pdsmart/MZ80A_RFS/docs/20200314152534.png

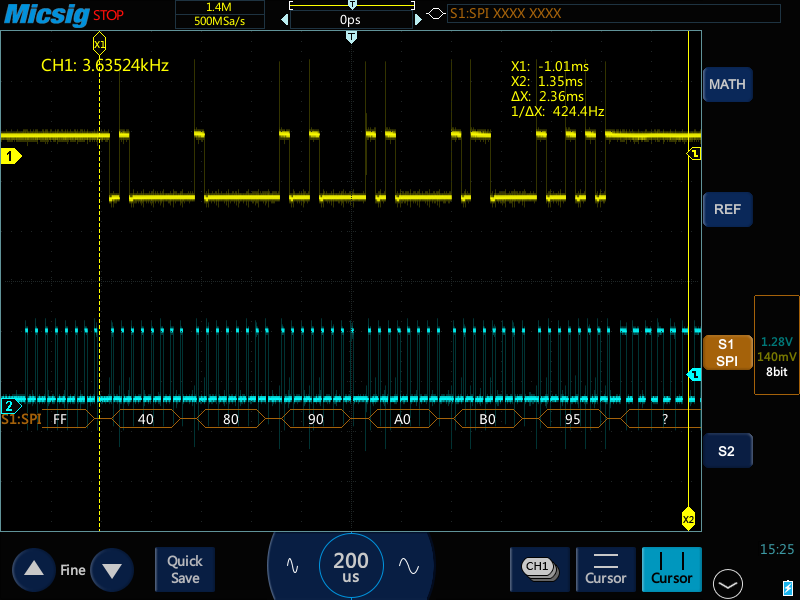
docs/20200314152534.png
