pdsmart/MZ80A_RFS/software/asm/RFSBASIC.asm

;-----------------------------------------------------------------------------------------------
; NASCOM ROM BASIC Ver 4.7, (C) 1978 Microsoft
; Scanned from source published in 80-BUS NEWS from Vol 2, Issue 3
; (May-June 1983) to Vol 3, Issue 3 (May-June 1984)
; Adapted for the freeware Zilog Macro Assembler 2.10 to produce
; the original ROM code (checksum A934H). PA
;
; This BASIC has been created from the original NASCOM v4.7b source and also
; may have elements of Grant Searle's changes as both were used in creating this
; version.
;
; It has undergone extensive modification:
; 1. Restore the CLOAD/CSAVE commands. These commands load/save tokenised cassette
;    images. The cassette images are from the NASCOM but converted with the
;    'nasconv' C program which removes the tape formatting, updates the token values
;    and address pointers.
; 2. Add LOAD/SAVE commands. These commands load/save BASIC in text format.
; 3. Restored the SCREEN command so it works with the Sharp MZ80A 40/80 column screen.
; 4. Increased the command word table to allow additional commands which I expect to add.
; I've added additional comments as things have been figured out to aid future understanding.
;
; Thus (C)opyright notices:
; Original source is: (C) 1978 Microsoft
; Updates (some reversed out): Grant Searle, http://searle.hostei.com/grant/index.html
;                                            eMail: home.micros01@btinternet.com
; All other updates (C) Philip Smart, 2020. http://www.eaw.app philip.smart\@net2net.org
;-----------------------------------------------------------------------------------------------


            ; Bring in additional resources.
            INCLUDE "BASIC_Definitions.asm"
            INCLUDE "Macros.asm"

            ; Sharp MZ-80A Tape Format Header - used by all software including RFS/TZFS 
            ; in processing/loading of this file.
            ;
            ORG     10F0h

            DB      01h                                                                                     ; Code Type, 01 = Machine Code.
HEADER1:    IF BUILD_MZ80A = 1
            DB      "MZ80A BASIC V1.1", 0DH                                                                 ; Title/Name (17 bytes).
            DW      CODEEND - CODESTART                                                                     ; Size of program.
            DW      CODESTART                                                                               ; Load address of program.
            DW      CODESTART                                                                               ; Exec address of program.
            ENDIF

HEADER2:    IF BUILD_RFS = 1
            DB      "RFS BASIC V1.1" , 0DH, 0DH, 0DH                                                        ; Title/Name (17 bytes).
            DW      (CODEEND - CODESTART) + (RELOCEND - RELOC) + (RELOCRFS2END - RELOCRFS2)                 ; Size of program.
            DW      01200H                                                                                  ; Load address of program.
            DW      RELOCRFS                                                                                ; Exec address of program.
            ENDIF

HEADER3:    IF BUILD_TZFS = 1
            DB      "RFS BASIC V1.1 ", 0DH, 0DH                                                             ; Title/Name (17 bytes).
            DW      (CODEEND - CODESTART) + (RELOCEND - RELOC)                                              ; Size of program.
            DW      01200H                                                                                  ; Load address of program.
            DW      RELOC                                                                                   ; Exec address of program.
            ENDIF

            DB      00h, 00h, 00h, 00h, 00h, 00h, 00h, 00h, 00h, 00h, 00h, 00h, 00h, 00h, 00h, 00h          ; Comment (104 bytes).
            DB      00h, 00h, 00h, 00h, 00h, 00h, 00h, 00h, 00h, 00h, 00h, 00h, 00h, 00h, 00h, 00h
            DB      00h, 00h, 00h, 00h, 00h, 00h, 00h, 00h, 00h, 00h, 00h, 00h, 00h, 00h, 00h, 00h
            DB      00h, 00h, 00h, 00h, 00h, 00h, 00h, 00h, 00h, 00h, 00h, 00h, 00h, 00h, 00h, 00h
            DB      00h, 00h, 00h, 00h, 00h, 00h, 00h, 00h, 00h, 00h, 00h, 00h, 00h, 00h, 00h, 00h
            DB      00h, 00h, 00h, 00h, 00h, 00h, 00h, 00h, 00h, 00h, 00h, 00h, 00h, 00h, 00h, 00h
            DB      00h, 00h, 00h, 00h, 00h, 00h, 00h, 00h

            ; Load address of this program when first loaded.
            ;
BUILD1:     IF BUILD_MZ80A = 1
            ORG     1200H
            ENDIF

BUILD2:     IF BUILD_TZFS+BUILD_RFS > 0
            ORG     0000H
            ENDIF

CODESTART:

COLD:       JP      STARTB               ; Jump for cold start
WARM:       JP      WARMST               ; Jump for warm start
STARTB:     
            LD      IX,0                 ; Flag cold start
            JP      CSTART               ; Jump to initialise

            DW      DEINT                ; Get integer -32768 to 32767
            DW      ABPASS               ; Return integer in AB


VECTORS:    IF BUILD_TZFS+BUILD_RFS > 0
            ALIGN   0038H
            ORG     0038H
INTVEC:     DS      3                    ; Space for the Interrupt vector.

            ALIGN   0066H
            ORG     0066H
NMIVEC:     DS      3                    ; Space for the NMI vector.
            ENDIF

CSTART:     DI                           ; Disable Interrupts and sat mode. NB. Interrupts are physically disabled by 8255 Port C2 set to low.
            IM      1
            LD      SP,STACK             ; Start of workspace RAM

MEMSW0:     IF BUILD_TZFS+BUILD_RFS > 0
            LD      A,TZMM_MZ700_0       ; Ensure the top part of RAM is set to use the mainboard as we need to configure hardware.
            OUT     (MMCFG),A
            ENDIF

INITST:     LD      A,0                  ; Clear break flag
            LD      (BRKFLG),A

            LD      HL,GVARSTART         ; Start of global variable area
            LD      BC,GVAREND-GVARSTART ; Size of global variable area.
            XOR     A
            LD      D,A
INIT1:      LD      (HL),D               ; Clear variable memory including stack space.
            INC     HL
            DEC     BC
            LD      A,B
            OR      C
            JR      NZ,INIT1
            ;
            CALL    MODE                 ; Configure 8255 port C, set Motor Off, VGATE to 1 (off) and INTMSK to 0 (interrupts disabled).
            LD      A,000H               ; Clear the screen buffer.
            LD      HL,SCRN
            CALL    CLR8
            LD      A,017H               ; Blue background, white characters in colour mode. Bit 7 is set as a write to bit 7 @ DFFFH selects 80Char mode.
            LD      HL,ARAM
            CALL    CLR8
            LD      A,004H
            LD      (TEMPW),A            ; Setup the tempo for sound output.

INIT3:      ; Setup keyboard buffer control.
            LD      A,0
            LD      (KEYCOUNT),A         ; Set keyboard buffer to empty.
            LD      HL,KEYBUF
            LD      (KEYWRITE),HL        ; Set write pointer to beginning of keyboard buffer.
            LD      (KEYREAD),HL         ; Set read pointer to beginning of keyboard buffer.

            ; Setup keyboard rate control and set to CAPSLOCK mode.
            ; (0 = Off, 1 = CAPSLOCK, 2 = SHIFTLOCK).
            LD      A,000H               ; Initialise key repeater.
            LD      (KEYRPT),A
            LD      A,001H
            LD      (SFTLK),A            ; Setup shift lock, default = off.

            ; Setup the initial cursor, for CAPSLOCK this is a double underscore.
            LD      A,03EH
            LD      (FLSDT),A
            LD      A,080H               ; Cursor on (Bit D7=1).
            LD      (FLASHCTL),A

            ; Change to 80 character mode.
            LD      HL,DSPCTL            ; Setup address of display control register latch.
            LD      A, 128               ; 80 char mode.
            LD      E,(HL)               ; Dummy operation to enable latch write via multivibrator.
            LD      (HL), A
            CALL    MLDSP
            CALL    BEL                  ; Beep to indicate startup - for cases where screen is slow to startup.
            LD      A,0FFH
            LD      (SWRK),A

INITANSI:   IF INCLUDE_ANSITERM = 1      ; If the ansi terminal emulator is builtin, enable it as default.
            LD      (ANSIENABLE),A
            ENDIF

            ; Setup timer interrupts
            LD      IX,TIMIN             ; Pass the interrupt service handler vector.
            LD      BC,00000H            ; Time starts at 00:00:00 01/01/1980 on initialisation.
            LD      DE,00000H
            LD      HL,00000H
            CALL    TIMESET
            ;
            LD      A,05H                ; Enable interrupts at hardware level, this must be done before switching memory mode.
            LD      (KEYPF),A
            ;
MEMSW1:     IF BUILD_TZFS+BUILD_RFS > 0
            LD      A,TZMM_MZ700_2       ; Enable the full 64K memory range before starting BASIC initialisation.
            OUT     (MMCFG),A
            ENDIF

            ; Clear memory
            LD      HL,WRKSPC
MEMSZ1:     IF BUILD_MZ80A = 1
            LD      BC,MAXMEM - WRKSPC   ; Clear to top of physical RAM.
            ENDIF
MEMSZ2:     IF BUILD_TZFS+BUILD_RFS > 0
            LD      BC,10000H - WRKSPC   ; Clear to top of physical RAM.
            ENDIF
            LD      E,00H
INIT4:      LD      (HL),E
            INC     HL
            DEC     BC
            LD      A,B
            OR      C
            JR      NZ,INIT4
            ;
            EI
            ;
INIT:       LD      DE,INITAB            ; Initialise workspace
            LD      B,INITBE-INITAB+3    ; Bytes to copy
            LD      HL,WRKSPC            ; Into workspace RAM
COPY:       LD      A,(DE)               ; Get source
            LD      (HL),A               ; To destination
            INC     HL                   ; Next destination
            INC     DE                   ; Next source
            DEC     B                    ; Count bytes
            JP      NZ,COPY              ; More to move
       ;    LD      SP,HL                ; Temporary stack
            CALL    CLREG                ; Clear registers and stack
            CALL    PRNTCRLF             ; Output CRLF
            LD      (BUFFER+72+1),A      ; Mark end of buffer
            LD      (PROGST),A           ; Initialise program area

            LD      HL,MAXMEM
            LD      DE,0-50              ; 50 Bytes string space
            LD      (LSTRAM),HL          ; Save last available RAM
            ADD     HL,DE                ; Allocate string space
            LD      (STRSPC),HL          ; Save string space
            CALL    CLRPTR               ; Clear program area
            LD      HL,(STRSPC)          ; Get end of memory
            LD      DE,0-17              ; Offset for free bytes
            ADD     HL,DE                ; Adjust HL
            LD      DE,PROGST            ; Start of program text
            LD      A,L                  ; Get LSB
            SUB     E                    ; Adjust it
            LD      L,A                  ; Re-save
            LD      A,H                  ; Get MSB
            SBC     A,D                  ; Adjust it
            LD      H,A                  ; Re-save
            PUSH    HL                   ; Save bytes free
            CALL    CLS                  ; Clear screen and initialise the screen variables
            LD      HL,SIGNON            ; Sign-on message
            CALL    PRS                  ; Output string
            POP     HL                   ; Get bytes free back
            CALL    PRNTHL               ; Output amount of free memory
            LD      HL,BFREE             ; " Bytes free" message
            CALL    PRS                  ; Output string

WARMST:     LD      SP,STACK             ; Temporary stack
BRKRET:     CALL    CLREG                ; Clear registers and stack
            JP      PRNTOK               ; Go to get command line

            ; FUNCTION ADDRESS TABLE

FNCTAB:     DW      SGN
            DW      INT
            DW      ABS
            DW      USR
            DW      FRE
            DW      INP
            DW      POS
            DW      SQR
            DW      RND
            DW      LOG
            DW      EXP
            DW      COS
            DW      SIN
            DW      TAN
            DW      ATN
            DW      PEEK
            DW      DEEK
            DW      POINT
            DW      LEN
            DW      STR
            DW      VAL
            DW      ASC
            DW      CHR
            DW      HEX
            DW      BIN
            DW      LEFT
            DW      RIGHT
            DW      MID

            ; RESERVED WORD LIST

WORDS:      DB      'E'+80H,"ND"         ; 0x80
            DB      'F'+80H,"OR"         ; 0x81
            DB      'N'+80H,"EXT"        ; 0x82
            DB      'D'+80H,"ATA"        ; 0x83
            DB      'I'+80H,"NPUT"       ; 0x84
            DB      'D'+80H,"IM"         ; 0x85
            DB      'R'+80H,"EAD"        ; 0x86
            DB      'L'+80H,"ET"         ; 0x87
            DB      'G'+80H,"OTO"        ; 0x88
            DB      'R'+80H,"UN"         ; 0x89
            DB      'I'+80H,"F"          ; 0x8a
            DB      'R'+80H,"ESTORE"     ; 0x8b
            DB      'G'+80H,"OSUB"       ; 0x8c
            DB      'R'+80H,"ETURN"      ; 0x8d
            DB      'R'+80H,"EM"         ; 0x8e
            DB      'S'+80H,"TOP"        ; 0x8f
            DB      'O'+80H,"UT"         ; 0x90
            DB      'O'+80H,"N"          ; 0x91
            DB      'N'+80H,"ULL"        ; 0x92
            DB      'W'+80H,"AIT"        ; 0x93
            DB      'D'+80H,"EF"         ; 0x94
            DB      'P'+80H,"OKE"        ; 0x95
            DB      'D'+80H,"OKE"        ; 0x96
            DB      'S'+80H,"CREEN"      ; 0x97
            DB      'L'+80H,"INES"       ; 0x98
            DB      'C'+80H,"LS"         ; 0x99
            DB      'W'+80H,"IDTH"       ; 0x9a
            DB      'M'+80H,"ONITOR"     ; 0x9b
            DB      'S'+80H,"ET"         ; 0x9c
            DB      'R'+80H,"ESET"       ; 0x9d
            DB      'P'+80H,"RINT"       ; 0x9e
            DB      'C'+80H,"ONT"        ; 0x9f
            DB      'L'+80H,"IST"        ; 0xa0
            DB      'C'+80H,"LEAR"       ; 0xa1
            DB      'A'+80H,"NSITERM"    ; 0xa2

            ; Optional commands to be builtin when a tranZPUter board is present.
OPTIONS0:   IF BUILD_TZFS = 1
              DB    'C'+80H,"LOAD"       ; 0xa3
              DB    'C'+80H,"SAVE"       ; 0xa4
              DB    'L'+80H,"OAD"        ; 0xa5
              DB    'S'+80H,"AVE"        ; 0xa6 
              DB    'F'+80H,"REQ"        ; 0xa7
              DB    'D'+80H,"IR"         ; 0xa8  
              DB    'C'+80H,"D"          ; 0xa9 
            ENDIF
            IF BUILD_RFS = 1
              DB    'C'+80H,"LOAD"       ; 0xa3
              DB    'C'+80H,"SAVE"       ; 0xa4
              DB    'R'+80H,"EM"         ; 0xa5  
              DB    'R'+80H,"EM"         ; 0xa6  
              DB    'R'+80H,"EM"         ; 0xa7  
              DB    'R'+80H,"EM"         ; 0xa8  
              DB    'R'+80H,"EM"         ; 0xa9  
            ENDIF
            IF BUILD_MZ80A = 1
              DB    'C'+80H,"LOAD"       ; 0xa3
              DB    'C'+80H,"SAVE"       ; 0xa4
              DB    'R'+80H,"EM"         ; 0xa5  
              DB    'R'+80H,"EM"         ; 0xa6  
              DB    'R'+80H,"EM"         ; 0xa7  
              DB    'R'+80H,"EM"         ; 0xa8  
              DB    'R'+80H,"EM"         ; 0xa9  
            ENDIF
            DB      'N'+80H,"EW"         ; 0xaa    <- Command list terminator word, move to lowest command. Update the ZNEW variable below as well.
                                         ;         <- Reserved space for new commands.
            DB      'R'+80H,"EM"         ; 0xab  
            DB      'R'+80H,"EM"         ; 0xac  
            DB      'R'+80H,"EM"         ; 0xad  
            DB      'R'+80H,"EM"         ; 0xae  
            DB      'R'+80H,"EM"         ; 0xaf  
            DB      'R'+80H,"EM"         ; 0xb0  
            DB      'R'+80H,"EM"         ; 0xb1  
            DB      'R'+80H,"EM"         ; 0xb2  
            DB      'R'+80H,"EM"         ; 0xb3  
            DB      'R'+80H,"EM"         ; 0xb4  
            DB      'R'+80H,"EM"         ; 0xb5  
            DB      'R'+80H,"EM"         ; 0xb6  
            DB      'R'+80H,"EM"         ; 0xb7  
            DB      'R'+80H,"EM"         ; 0xb8  
            DB      'R'+80H,"EM"         ; 0xb9  
            DB      'R'+80H,"EM"         ; 0xba  
            DB      'R'+80H,"EM"         ; 0xbb  
            DB      'R'+80H,"EM"         ; 0xbc  
            DB      'R'+80H,"EM"         ; 0xbd  
            DB      'R'+80H,"EM"         ; 0xbe  
            DB      'R'+80H,"EM"         ; 0xbf  

            DB      'T'+80H,"AB("        ; 0xc0  <- 0xa5
            DB      'T'+80H,"O"          ; 0xc1  <- 0xa6
            DB      'F'+80H,"N"          ; 0xc2  <- 0xa7
            DB      'S'+80H,"PC("        ; 0xc3  <- 0xa8
            DB      'T'+80H,"HEN"        ; 0xc4  <- 0xa9
            DB      'N'+80H,"OT"         ; 0xc5  <- 0xaa
            DB      'S'+80H,"TEP"        ; 0xc6  <- 0xab

            DB      '+'+80H              ; 0xc7  <- 0xac
            DB      '-'+80H              ; 0xc8  <- 0xad
            DB      '*'+80H              ; 0xc9  <- 0xae
            DB      '/'+80H              ; 0xca  <- 0xaf
            DB      '^'+80H              ; 0xcb  <- 0xb0
            DB      'A'+80H,"ND"         ; 0xcc  <- 0xb1
            DB      'O'+80H,"R"          ; 0xcd  <- 0xb2
            DB      '>'+80H              ; 0xce  <- 0xb3
            DB      '='+80H              ; 0xcf  <- 0xb4
            DB      '<'+80H              ; 0xd0  <- 0xb5

            DB      'S'+80H,"GN"         ; 0xd1  <- 0xb6
            DB      'I'+80H,"NT"         ; 0xd2  <- 0xb7
            DB      'A'+80H,"BS"         ; 0xd3  <- 0xb8
            DB      'U'+80H,"SR"         ; 0xd4  <- 0xb9
            DB      'F'+80H,"RE"         ; 0xd5  <- 0xba
            DB      'I'+80H,"NP"         ; 0xd6  <- 0xbb
            DB      'P'+80H,"OS"         ; 0xd7  <- 0xbc
            DB      'S'+80H,"QR"         ; 0xd8  <- 0xbd
            DB      'R'+80H,"ND"         ; 0xd9  <- 0xbe
            DB      'L'+80H,"OG"         ; 0xda  <- 0xbf
            DB      'E'+80H,"XP"         ; 0xdb  <- 0xc0
            DB      'C'+80H,"OS"         ; 0xdc  <- 0xc1
            DB      'S'+80H,"IN"         ; 0xdd  <- 0xc2
            DB      'T'+80H,"AN"         ; 0xde  <- 0xc3
            DB      'A'+80H,"TN"         ; 0xdf  <- 0xc4
            DB      'P'+80H,"EEK"        ; 0xe0  <- 0xc5
            DB      'D'+80H,"EEK"        ; 0xe1  <- 0xc6
            DB      'P'+80H,"OINT"       ; 0xe2  <- 0xc7
            DB      'L'+80H,"EN"         ; 0xe3  <- 0xc8
            DB      'S'+80H,"TR$"        ; 0xe4  <- 0xc9
            DB      'V'+80H,"AL"         ; 0xe5  <- 0xca
            DB      'A'+80H,"SC"         ; 0xe6  <- 0xcb
            DB      'C'+80H,"HR$"        ; 0xe7  <- 0xcc
            DB      'H'+80H,"EX$"        ; 0xe8  <- 0xcd
            DB      'B'+80H,"IN$"        ; 0xe9  <- 0xce
            DB      'L'+80H,"EFT$"       ; 0xea  <- 0xcf
            DB      'R'+80H,"IGHT$"      ; 0xeb  <- 0xd0
            DB      'M'+80H,"ID$"        ; 0xec  <- 0xd1
            DB      80H                  ; End of list marker

            ; KEYWORD ADDRESS TABLE

WORDTB:     DW      PEND
            DW      FOR
            DW      NEXT
            DW      DATA
            DW      INPUT
            DW      DIM
            DW      READ
            DW      LET
            DW      GOTO
            DW      RUN
            DW      IF
            DW      RESTOR
            DW      GOSUB
            DW      RETURN
            DW      REM
            DW      STOP
            DW      POUT
            DW      ON
            DW      NULL
            DW      WAIT
            DW      DEF
            DW      POKE
            DW      DOKE
            DW      SCREEN
            DW      LINES
            DW      CLS
            DW      WIDTH
            DW      MONITR
            DW      PSET
            DW      RESET
            DW      PRINT
            DW      CONT
            DW      LIST
            DW      CLEAR
            DW      SETANSITERM          ; Enable/disable the ANSI Terminal Emulator.

            ; Optional commands to be builtin when a tranZPUter board is present.
OPTIONS1:   IF BUILD_TZFS = 1
            DW      CLOADTZ              ; Load tokenised BASIC program.
            DW      CSAVETZ              ; Save tokenised BASIC program.
            DW      LOAD                 ; Load ASCII text BASIC program.
            DW      SAVE                 ; Save BASIC as ASCII text.
            DW      SETFREQ              ; Set the CPU Frequency.    
            DW      DIRSDCARD            ; List out the SD directory.
            DW      SETDIR               ; Change directory for all load and save operations.
            ENDIF
OPTIONS2:   IF BUILD_RFS = 1
            DW      CLOAD80A             ; Load tokenised BASIC program from tape.
            DW      CSAVE80A             ; Save tokenised BASIC program to tape.
            DW      REM
            DW      REM
            DW      REM
            DW      REM
            DW      REM
            ENDIF
OPTIONS3:   IF BUILD_MZ80A = 1
            DW      CLOAD80A             ; Load tokenised BASIC program from tape.
            DW      CSAVE80A             ; Save tokenised BASIC program to tape.
            DW      REM
            DW      REM
            DW      REM
            DW      REM
            DW      REM
            ENDIF
            DW      NEW

            ; RESERVED WORD TOKEN VALUES

ZEND        EQU     080H                 ; END    - ZEND marks the start of the table.
ZFOR        EQU     081H                 ; FOR
ZDATA       EQU     083H                 ; DATA
ZGOTO       EQU     088H                 ; GOTO
ZGOSUB      EQU     08CH                 ; GOSUB
ZREM        EQU     08EH                 ; REM
ZPRINT      EQU     09EH                 ; PRINT
ZNEW        EQU     0AAH                 ; NEW    - ZNEW marks the end of the table
                                         ; AA..BF are reserved for future commands.

            ; Space for expansion, a block of tokens for commands has been created from 0xA5 to 0xBF.

FUNCSTRT    EQU     0C0H                 ; Function start.
ZTAB        EQU     FUNCSTRT + 00H       ; 0A5H            ; TAB
ZTO         EQU     FUNCSTRT + 01H       ; 0A6H            ; TO
ZFN         EQU     FUNCSTRT + 02H       ; 0A7H            ; FN
ZSPC        EQU     FUNCSTRT + 03H       ; 0A8H            ; SPC
ZTHEN       EQU     FUNCSTRT + 04H       ; 0A9H            ; THEN
ZNOT        EQU     FUNCSTRT + 05H       ; 0AAH            ; NOT
ZSTEP       EQU     FUNCSTRT + 06H       ; 0ABH            ; STEP

ZPLUS       EQU     FUNCSTRT + 07H       ; 0ACH            ; +
ZMINUS      EQU     FUNCSTRT + 08H       ; 0ADH            ; -
ZTIMES      EQU     FUNCSTRT + 09H       ; 0AEH            ; *
ZDIV        EQU     FUNCSTRT + 0AH       ; 0AFH            ; /
                                         ; 0B0H
                                         ; 0B1H
ZOR         EQU     FUNCSTRT + 0dH       ; 0B2H            ; OR
ZGTR        EQU     FUNCSTRT + 0eH       ; 0B3H            ; >
ZEQUAL      EQU     FUNCSTRT + 0fH       ; 0B4H            ; M
ZLTH        EQU     FUNCSTRT + 10H       ; 0B5H            ; <
ZSGN        EQU     FUNCSTRT + 11H       ; 0B6H            ; SGN
                                         ; 0B7H
                                         ; 0B8H
                                         ; 0B9H
                                         ; 0BAH
                                         ; 0BBH
                                         ; 0BCH
                                         ; 0BDH
                                         ; 0BEH
                                         ; 0BFH
                                         ; 0C0H
                                         ; 0C1H
                                         ; 0C2H
                                         ; 0C3H
                                         ; 0C4H
                                         ; 0C5H
                                         ; 0C6H
ZPOINT      EQU     FUNCSTRT + 22H       ; 0C7H            ; POINT
                                         ; 0C8H
                                         ; 0C9H
                                         ; 0CAH
                                         ; 0CBH
                                         ; 0CCH
ZLEFT       EQU     FUNCSTRT + 2aH       ; 0CFH            ; LEFT$

            ; Space for expansion, reserve a block of tokens for functions.


            ; ARITHMETIC PRECEDENCE TABLE

PRITAB:     DB      79H                  ; Precedence value
            DW      PADD                 ; FPREG = <last> + FPREG

            DB      79H                  ; Precedence value
            DW      PSUB                 ; FPREG = <last> - FPREG

            DB      7CH                  ; Precedence value
            DW      MULT                 ; PPREG = <last> * FPREG

            DB      7CH                  ; Precedence value
            DW      DIV                  ; FPREG = <last> / FPREG

            DB      7FH                  ; Precedence value
            DW      POWER                ; FPREG = <last> ^ FPREG

            DB      50H                  ; Precedence value
            DW      PAND                 ; FPREG = <last> AND FPREG

            DB      46H                  ; Precedence value
            DW      POR                  ; FPREG = <last> OR FPREG

            ; BASIC ERROR CODE LIST

ERRORS:     DB      "NF"                 ; NEXT without FOR
            DB      "SN"                 ; Syntax error
            DB      "RG"                 ; RETURN without GOSUB
            DB      "OD"                 ; Out of DATA
            DB      "FC"                 ; Illegal function call
            DB      "OV"                 ; Overflow error
            DB      "OM"                 ; Out of memory
            DB      "UL"                 ; Undefined line
            DB      "BS"                 ; Bad subscript
            DB      "DD"                 ; Re-DIMensioned array
            DB      "/0"                 ; Division by zero
            DB      "ID"                 ; Illegal direct
            DB      "TM"                 ; Type mis-match
            DB      "OS"                 ; Out of string space
            DB      "LS"                 ; String too long
            DB      "ST"                 ; String formula too complex
            DB      "CN"                 ; Can't CONTinue
            DB      "UF"                 ; Undefined FN function
            DB      "MO"                 ; Missing operand
            DB      "HX"                 ; HEX error
            DB      "BN"                 ; BIN error
            DB      "BV"                 ; Bad Value
            DB      "IO"                 ; IO error

            ; INITIALISATION TABLE -------------------------------------------------------

INITAB:     JP      WARMST               ; Warm start jump
            JP      FCERR                ; "USR (X)" jump (Set to Error)

            OUT     (0),A                ; "OUT p,n" skeleton
            RET

            SUB     0                    ; Division support routine
            LD      L,A
            LD      A,H
            SBC     A,0
            LD      H,A
            LD      A,B
            SBC     A,0
            LD      B,A
            LD      A,0
            RET

            DB      0,0,0                ; Random number seed
                                         ; Table used by RND
            DB      035H,04AH,0CAH,099H  ;-2.65145E+07
            DB      039H,01CH,076H,098H  ; 1.61291E+07
            DB      022H,095H,0B3H,098H  ;-1.17691E+07
            DB      00AH,0DDH,047H,098H  ; 1.30983E+07
            DB      053H,0D1H,099H,099H  ;-2-01612E+07
            DB      00AH,01AH,09FH,098H  ;-1.04269E+07
            DB      065H,0BCH,0CDH,098H  ;-1.34831E+07
            DB      0D6H,077H,03EH,098H  ; 1.24825E+07
            DB      052H,0C7H,04FH,080H  ; Last random number

            IN      A,(0)                ; INP (x) skeleton
            RET

            DB      1                    ; POS (x) number (1)
INITABW:    DB      COLW                 ; Terminal width
            DB      28                   ; Width for commas (3 columns)
            DB      0                    ; No nulls after input bytes
            DB      0                    ; Output enabled (^O off)

            DW      20                   ; Initial lines counter
            DW      20                   ; Initial lines number
            DW      0                    ; Array load/save check sum

            DB      0                    ; Break not by NMI
            DB      0                    ; Break flag

            JP      TTYLIN               ; Input reflection (set to TTY)
            JP      0000H                ; POINT reflection unused
            JP      0000H                ; SET reflection
            JP      0000H                ; RESET reflection
           ;JP      POINTB               ; POINT reflection unused
           ;JP      SETB                 ; SET reflection
           ;JP      RESETB               ; RESET reflection

            DW      STLOOK               ; Temp string space
            DW      -2                   ; Current line number (cold)
            DW      PROGST+1             ; Start of program text
INITBE:                                  ; END OF INITIALISATION TABLE

            ; END OF INITIALISATION TABLE ---------------------------------------------------

ERRMSG:     DB      " Error",0
INMSG:      DB      " in ",0
ZERBYT      EQU     $-1                  ; A zero byte
OKMSG:      DB      "Ok",CR,LF,0,0
BRKMSG:     DB      "Break",0

BAKSTK:     LD      HL,4                 ; Look for "FOR" block with
            ADD     HL,SP                ; same index as specified
LOKFOR:     LD      A,(HL)               ; Get block ID
            INC     HL                   ; Point to index address
            CP      ZFOR                 ; Is it a "FOR" token
            RET     NZ                   ; No - exit
            LD      C,(HL)               ; BC = Address of "FOR" index
            INC     HL
            LD      B,(HL)
            INC     HL                   ; Point to sign of STEP
            PUSH    HL                   ; Save pointer to sign
            LD      L,C                  ; HL = address of "FOR" index
            LD      H,B
            LD      A,D                  ; See if an index was specified
            OR      E                    ; DE = 0 if no index specified
            EX      DE,HL                ; Specified index into HL
            JP      Z,INDFND             ; Skip if no index given
            EX      DE,HL                ; Index back into DE
            CALL    CPDEHL               ; Compare index with one given
INDFND:     LD      BC,16-3              ; Offset to next block
            POP     HL                   ; Restore pointer to sign
            RET     Z                    ; Return if block found
            ADD     HL,BC                ; Point to next block
            JP      LOKFOR               ; Keep on looking

MOVUP:      CALL    ENFMEM               ; See if enough memory
MOVSTR:     PUSH    BC                   ; Save end of source
            EX      (SP),HL              ; Swap source and dest" end
            POP     BC                   ; Get end of destination
MOVLP:      CALL    CPDEHL               ; See if list moved
            LD      A,(HL)               ; Get byte
            LD      (BC),A               ; Move it
            RET     Z                    ; Exit if all done
            DEC     BC                   ; Next byte to move to
            DEC     HL                   ; Next byte to move
            JP      MOVLP                ; Loop until all bytes moved

CHKSTK:     PUSH    HL                   ; Save code string address
            LD      HL,(ARREND)          ; Lowest free memory
            LD      B,0                  ; BC = Number of levels to test
            ADD     HL,BC                ; 2 Bytes for each level
            ADD     HL,BC
            DB      3EH                  ; Skip "PUSH HL"
ENFMEM:     PUSH    HL                   ; Save code string address
            LD      A,0D0H ;LOW -48      ; 48 Bytes minimum RAM
            SUB     L
            LD      L,A
            LD      A,0FFH               ; HIGH (-48) ; 48 Bytes minimum RAM
            SBC     A,H
            JP      C,OMERR              ; Not enough - ?OM Error
            LD      H,A
            ADD     HL,SP                ; Test if stack is overflowed
            POP     HL                   ; Restore code string address
            RET     C                    ; Return if enough mmory
OMERR:      LD      E,OM                 ; ?OM Error
            JP      BERROR

DATSNR:     LD      HL,(DATLIN)          ; Get line of current DATA item
            LD      (LINEAT),HL          ; Save as current line
SNERR:      LD      E,SN                 ; ?SN Error
            DB      01H                  ; Skip "LD E,DZ"
DZERR:      LD      E,DZ                 ; ?/0 Error
            DB      01H                  ; Skip "LD E,NF"
NFERR:      LD      E,NF                 ; ?NF Error
            DB      01H                  ; Skip "LD E,DD"
DDERR:      LD      E,DDA                ; ?DD Error
            DB      01H                  ; Skip "LD E,UF"
UFERR:      LD      E,UF                 ; ?UF Error
            DB      01H                  ; Skip "LD E,OV
OVERR:      LD      E,OV                 ; ?OV Error
            DB      01H                  ; Skip "LD E,TM"
TMERR:      LD      E,TM                 ; ?TM Error

BERROR:     CALL    CLREG                ; Clear registers and stack
            LD      (CTLOFG),A           ; Enable output (A is 0)
            CALL    STTLIN               ; Start new line
            LD      HL,ERRORS            ; Point to error codes
            LD      D,A                  ; D = 0 (A is 0)
            LD      A,'?'
            CALL    OUTC                 ; Output '?'
            ADD     HL,DE                ; Offset to correct error code
            LD      A,(HL)               ; First character
            CALL    OUTC                 ; Output it
            CALL    GETCHR               ; Get next character
            CALL    OUTC                 ; Output it
            LD      HL,ERRMSG            ; "Error" message
ERRIN:      CALL    PRS                  ; Output message
            LD      HL,(LINEAT)          ; Get line of error
            LD      DE,-2                ; Cold start error if -2
            CALL    CPDEHL               ; See if cold start error
            JP      Z,CSTART             ; Cold start error - Restart
            LD      A,H                  ; Was it a direct error?
            AND     L                    ; Line = -1 if direct error
            INC     A
            CALL    NZ,LINEIN            ; No - output line of error
            DB      3EH                  ; Skip "POP BC"
POPNOK:     POP     BC                   ; Drop address in input buffer

PRNTOK:     XOR     A                    ; Output "Ok" and get command
            LD      (CTLOFG),A           ; Enable output
            CALL    STTLIN               ; Start new line
            LD      HL,OKMSG             ; "Ok" message
            CALL    PRS                  ; Output "Ok"
GETCMD:     LD      HL,-1                ; Flag direct mode
            LD      (LINEAT),HL          ; Save as current line
            CALL    GETLIN               ; Get an input line
            JP      C,GETCMD             ; Get line again if break
            CALL    GETCHR               ; Get first character
            INC     A                    ; Test if end of line
            DEC     A                    ; Without affecting Carry
            JP      Z,GETCMD             ; Nothing entered - Get another
            PUSH    AF                   ; Save Carry status
            CALL    ATOH                 ; Get line number into DE
            PUSH    DE                   ; Save line number
            CALL    CRUNCH               ; Tokenise rest of line
            LD      B,A                  ; Length of tokenised line -> length is in C, B is zeroed.
            POP     DE                   ; Restore line number
            POP     AF                   ; Restore Carry
            JP      NC,EXCUTE            ; No line number - Direct mode
            PUSH    DE                   ; Save line number
            PUSH    BC                   ; Save length of tokenised line
            XOR     A
            LD      (LSTBIN),A           ; Clear last byte input
            CALL    GETCHR               ; Get next character
            OR      A                    ; Set flags
            PUSH    AF                   ; And save them
            CALL    SRCHLN               ; Search for line number in DE
            JP      C,LINFND             ; Jump if line found
            POP     AF                   ; Get status
            PUSH    AF                   ; And re-save
            JP      Z,ULERR              ; Nothing after number - Error
            OR      A                    ; Clear Carry
LINFND:     PUSH    BC                   ; Save address of line in prog
            JP      NC,INEWLN            ; Line not found - Insert new
            EX      DE,HL                ; Next line address in DE
            LD      HL,(PROGND)          ; End of program
SFTPRG:     LD      A,(DE)               ; Shift rest of program down
            LD      (BC),A
            INC     BC                   ; Next destination
            INC     DE                   ; Next source
            CALL    CPDEHL               ; All done?
            JP      NZ,SFTPRG            ; More to do
            LD      H,B                  ; HL - New end of program
            LD      L,C
            LD      (PROGND),HL          ; Update end of program

INEWLN:     POP     DE                   ; Get address of line,
            POP     AF                   ; Get status
            JP      Z,SETPTR             ; No text - Set up pointers
            LD      HL,(PROGND)          ; Get end of program
            EX      (SP),HL              ; Get length of input line
            POP     BC                   ; End of program to BC
            ADD     HL,BC                ; Find new end
            PUSH    HL                   ; Save new end
            CALL    MOVUP                ; Make space for line
            POP     HL                   ; Restore new end
            LD      (PROGND),HL          ; Update end of program pointer
            EX      DE,HL                ; Get line to move up in HL
            LD      (HL),H               ; Save MSB
            POP     DE                   ; Get new line number
            INC     HL                   ; Skip pointer
            INC     HL
            LD      (HL),E               ; Save LSB of line number
            INC     HL
            LD      (HL),D               ; Save MSB of line number
            INC     HL                   ; To first byte in line
            LD      DE,BUFFER            ; Copy buffer to program
MOVBUF:     LD      A,(DE)               ; Get source
            LD      (HL),A               ; Save destinations
            INC     HL                   ; Next source
            INC     DE                   ; Next destination
            OR      A                    ; Done?
            JP      NZ,MOVBUF            ; No - Repeat
SETPTR:     CALL    RUNFST               ; Set line pointers
            INC     HL                   ; To LSB of pointer
            EX      DE,HL                ; Address to DE
PTRLP:      LD      H,D                  ; Address to HL
            LD      L,E
            LD      A,(HL)               ; Get LSB of pointer
            INC     HL                   ; To MSB of pointer
            OR      (HL)                 ; Compare with MSB pointer
            JP      Z,GETCMD             ; Get command line if end
            INC     HL                   ; To LSB of line number
            INC     HL                   ; Skip line number
            INC     HL                   ; Point to first byte in line
            XOR     A                    ; Looking for 00 byte
FNDEND:     CP      (HL)                 ; Found end of line?
            INC     HL                   ; Move to next byte
            JP      NZ,FNDEND            ; No - Keep looking
            EX      DE,HL                ; Next line address to HL
            LD      (HL),E               ; Save LSB of pointer
            INC     HL
            LD      (HL),D               ; Save MSB of pointer
            JP      PTRLP                ; Do next line

SRCHLN:     LD      HL,(BASTXT)          ; Start of program text
SRCHLP:     LD      B,H                  ; BC = Address to look at
            LD      C,L
            LD      A,(HL)               ; Get address of next line
            INC     HL
            OR      (HL)                 ; End of program found?
            DEC     HL
            RET     Z                    ; Yes - Line not found
            INC     HL
            INC     HL
            LD      A,(HL)               ; Get LSB of line number
            INC     HL
            LD      H,(HL)               ; Get MSB of line number
            LD      L,A
            CALL    CPDEHL               ; Compare with line in DE
            LD      H,B                  ; HL = Start of this line
            LD      L,C
            LD      A,(HL)               ; Get LSB of next line address
            INC     HL
            LD      H,(HL)               ; Get MSB of next line address
            LD      L,A                  ; Next line to HL
            CCF
            RET     Z                    ; Lines found - Exit
            CCF
            RET     NC                   ; Line not found,at line after
            JP      SRCHLP               ; Keep looking

NEW:        RET     NZ                   ; Return if any more on line
CLRPTR:     LD      HL,(BASTXT)          ; Point to start of program
            XOR     A                    ; Set program area to empty
            LD      (HL),A               ; Save LSB = 00
            INC     HL
            LD      (HL),A               ; Save MSB = 00
            INC     HL
            LD      (PROGND),HL          ; Set program end

RUNFST:     LD      HL,(BASTXT)          ; Clear all variables
            DEC     HL

INTVAR:     LD      (BRKLIN),HL          ; Initialise RUN variables
            LD      HL,(LSTRAM)          ; Get end of RAM
            LD      (STRBOT),HL          ; Clear string space
            XOR     A
            CALL    RESTOR               ; Reset DATA pointers
            LD      HL,(PROGND)          ; Get end of program
            LD      (VAREND),HL          ; Clear variables
            LD      (ARREND),HL          ; Clear arrays

CLREG:      POP     BC                   ; Save return address
            LD      HL,(STRSPC)          ; Get end of working RAN
            LD      SP,HL                ; Set stack
            LD      HL,TMSTPL            ; Temporary string pool
            LD      (TMSTPT),HL          ; Reset temporary string ptr
            XOR     A                    ; A = 00
            LD      L,A                  ; HL = 0000
            LD      H,A
            LD      (CONTAD),HL          ; No CONTinue
            LD      (FORFLG),A           ; Clear FOR flag
            LD      (FNRGNM),HL          ; Clear FN argument
            PUSH    HL                   ; HL = 0000
            PUSH    BC                   ; Put back return
DOAGN:      LD      HL,(BRKLIN)          ; Get address of code to RUN
            RET                          ; Return to execution driver

PROMPT:     LD      A,'?'                ; '?'
            CALL    OUTC                 ; Output character
            LD      A,' '                ; Space
            CALL    OUTC                 ; Output character
            JP      RINPUT               ; Get input line

CRUNCH:     XOR     A                    ; Tokenise line @ HL to BUFFER
            LD      (DATFLG),A           ; Reset literal flag
            LD      C,2+3                ; 2 byte number and 3 nulls
            LD      DE,BUFFER            ; Start of input buffer
CRNCLP:     LD      A,(HL)               ; Get byte
            CP      ' '                  ; Is it a space?
            JP      Z,MOVDIR             ; Yes - Copy direct
            LD      B,A                  ; Save character
            CP      '"'                  ; Is it a quote?
            JP      Z,CPYLIT             ; Yes - Copy literal string
            OR      A                    ; Is it end of buffer?
            JP      Z,ENDBUF             ; Yes - End buffer
            LD      A,(DATFLG)           ; Get data type
            OR      A                    ; Literal?
            LD      A,(HL)               ; Get byte to copy
            JP      NZ,MOVDIR            ; Literal - Copy direct
            CP      '?'                  ; Is it '?' short for PRINT
            LD      A,ZPRINT             ; "PRINT" token
            JP      Z,MOVDIR             ; Yes - replace it
            LD      A,(HL)               ; Get byte again
            CP      '0'                  ; Is it less than '0'
            JP      C,FNDWRD             ; Yes - Look for reserved words
            CP      60; ";"+1            ; Is it "0123456789:;" ?
            JP      C,MOVDIR             ; Yes - copy it direct
FNDWRD:     PUSH    DE                   ; Look for reserved words
            LD      DE,WORDS-1           ; Point to table
            PUSH    BC                   ; Save count
            LD      BC,RETNAD            ; Where to return to
            PUSH    BC                   ; Save return address
            LD      B,ZEND-1             ; First token value -1
            LD      A,(HL)               ; Get byte
            CP      'a'                  ; Less than 'a' ?
            JP      C,SEARCH             ; Yes - search for words
            CP      'z'+1                ; Greater than 'z' ?
            JP      NC,SEARCH            ; Yes - search for words
            AND     01011111B            ; Force upper case
            LD      (HL),A               ; Replace byte
SEARCH:     LD      C,(HL)               ; Search for a word
            EX      DE,HL
GETNXT:     INC     HL                   ; Get next reserved word
            OR      (HL)                 ; Start of word?
            JP      P,GETNXT             ; No - move on
            INC     B                    ; Increment token value
            LD      A, (HL)              ; Get byte from table
            AND     01111111B            ; Strip bit 7
            RET     Z                    ; Return if end of list
            CP      C                    ; Same character as in buffer?
            JP      NZ,GETNXT            ; No - get next word
            EX      DE,HL
            PUSH    HL                   ; Save start of word

NXTBYT:     INC     DE                   ; Look through rest of word
            LD      A,(DE)               ; Get byte from table
            OR      A                    ; End of word ?
            JP      M,MATCH              ; Yes - Match found
            LD      C,A                  ; Save it
            LD      A,B                  ; Get token value
            CP      ZGOTO                ; Is it "GOTO" token ?
            JP      NZ,NOSPC             ; No - Don't allow spaces
            CALL    GETCHR               ; Get next character
            DEC     HL                   ; Cancel increment from GETCHR
NOSPC:      INC     HL                   ; Next byte
            LD      A,(HL)               ; Get byte
            CP      'a'                  ; Less than 'a' ?
            JP      C,NOCHNG             ; Yes - don't change
            AND     01011111B            ; Make upper case
NOCHNG:     CP      C                    ; Same as in buffer ?
            JP      Z,NXTBYT             ; Yes - keep testing
            POP     HL                   ; Get back start of word
            JP      SEARCH               ; Look at next word

MATCH:      LD      C,B                  ; Word found - Save token value
            POP     AF                   ; Throw away return
            EX      DE,HL
            RET                          ; Return to "RETNAD"
RETNAD:     EX      DE,HL                ; Get address in string
            LD      A,C                  ; Get token value
            POP     BC                   ; Restore buffer length
            POP     DE                   ; Get destination address
MOVDIR:     INC     HL                   ; Next source in buffer
            LD      (DE),A               ; Put byte in buffer
            INC     DE                   ; Move up buffer
            INC     C                    ; Increment length of buffer
            SUB     ':'                  ; End of statement?
            JP      Z,SETLIT             ; Jump if multi-statement line
            CP      ZDATA-3AH            ; Is it DATA statement ?
            JP      NZ,TSTREM            ; No - see if REM
SETLIT:     LD      (DATFLG),A           ; Set literal flag
TSTREM:     SUB     ZREM-3AH             ; Is it REM?
            JP      NZ,CRNCLP            ; No - Leave flag
            LD      B,A                  ; Copy rest of buffer
NXTCHR:     LD      A,(HL)               ; Get byte
            OR      A                    ; End of line ?
            JP      Z,ENDBUF             ; Yes - Terminate buffer
            CP      B                    ; End of statement ?
            JP      Z,MOVDIR             ; Yes - Get next one
CPYLIT:     INC     HL                   ; Move up source string
            LD      (DE),A               ; Save in destination
            INC     C                    ; Increment length
            INC     DE                   ; Move up destination
            JP      NXTCHR               ; Repeat

ENDBUF:     LD      HL,BUFFER-1          ; Point to start of buffer
            LD      (DE),A               ; Mark end of buffer (A = 00)
            INC     DE
            LD      (DE),A               ; A = 00
            INC     DE
            LD      (DE),A               ; A = 00
            RET

DODEL:      LD      A,(NULFLG)           ; Get null flag status
            OR      A                    ; Is it zero?
            LD      A,0                  ; Zero A - Leave flags
            LD      (NULFLG),A           ; Zero null flag
            JP      NZ,ECHDEL            ; Set - Echo it
            DEC     B                    ; Decrement length
            JP      Z,GETLIN             ; Get line again if empty
            CALL    OUTC                 ; Output null character
            DB      3EH                  ; Skip "DEC B"
ECHDEL:     DEC     B                    ; Count bytes in buffer
            DEC     HL                   ; Back space buffer
            JP      Z,OTKLN              ; No buffer - Try again
            LD      A,(HL)               ; Get deleted byte
            CALL    OUTC                 ; Echo it
            JP      MORINP               ; Get more input

DELCHR:     DEC     B                    ; Count bytes in buffer
            DEC     HL                   ; Back space buffer
            CALL    OUTC                 ; Output character in A
            JP      NZ,MORINP            ; Not end - Get more
OTKLN:      CALL    OUTC                 ; Output character in A
KILIN:      CALL    PRNTCRLF             ; Output CRLF
            JP      TTYLIN               ; Get line again

GETLIN:
TTYLIN:     LD      HL,BUFFER            ; Get a line by character
            LD      B,1                  ; Set buffer as empty
            XOR     A
            LD      (NULFLG),A           ; Clear null flag
MORINP:     CALL    CLOTST               ; Get character and test ^O
            LD      C,A                  ; Save character in C
            CP      DELETE               ; Delete character?
            JP      Z,DODEL              ; Yes - Process it
            LD      A,(NULFLG)           ; Get null flag
            OR      A                    ; Test null flag status
            JP      Z,PROCES             ; Reset - Process character
            LD      A,0                  ; Set a null
            CALL    OUTC                 ; Output null
            XOR     A                    ; Clear A
            LD      (NULFLG),A           ; Reset null flag
PROCES:     LD      A,C                  ; Get character
            CP      CTRL_G               ; Bell?
            JP      Z,PUTCTL             ; Yes - Save it
            CP      CTRL_C               ; Is it control "C"?
            CALL    Z,PRNTCRLF           ; Yes - Output CRLF
            SCF                          ; Flag break
            RET     Z                    ; Return if control "C"
            CP      CR                   ; Is it enter?
            JP      Z,ENDINP             ; Yes - Terminate input
            CP      CTRL_U               ; Is it control "U"?
            JP      Z,KILIN              ; Yes - Get another line
            CP      '@'                  ; Is it "kill line"?
            JP      Z,OTKLN              ; Yes - Kill line
            CP      DELETE               ; Is it delete?
            JP      Z,DELCHR             ; Yes - Delete character
            CP      BACKS                ; Is it backspace?
            JP      Z,DELCHR             ; Yes - Delete character
            CP      CTRL_R               ; Is it control "R"?
            JP      NZ,PUTBUF            ; No - Put in buffer
            PUSH    BC                   ; Save buffer length
            PUSH    DE                   ; Save DE
            PUSH    HL                   ; Save buffer address
            LD      (HL),0               ; Mark end of buffer
            CALL    OUTNCR               ; Output and do CRLF
            LD      HL,BUFFER            ; Point to buffer start
            CALL    PRS                  ; Output buffer
            POP     HL                   ; Restore buffer address
            POP     DE                   ; Restore DE
            POP     BC                   ; Restore buffer length
            JP      MORINP               ; Get another character

PUTBUF:     CP      ' '                  ; Is it a control code?
            JP      C,MORINP             ; Yes - Ignore
PUTCTL:     LD      A,B                  ; Get number of bytes in buffer
            CP      72+1                 ; Test for line overflow
            LD      A,CTRL_G             ; Set a bell
            JP      NC,OUTNBS            ; Ring bell if buffer full
            LD      A,C                  ; Get character
            LD      (HL),C               ; Save in buffer
            LD      (LSTBIN),A           ; Save last input byte
            INC     HL                   ; Move up buffer
            INC     B                    ; Increment length
OUTIT:      CALL    OUTC                 ; Output the character entered
            JP      MORINP               ; Get another character

OUTNBS:     CALL    OUTC                 ; Output bell and back over it
            LD      A,BACKS              ; Set back space
            JP      OUTIT                ; Output it and get more

CPDEHL:     LD      A,H                  ; Get H
            SUB     D                    ; Compare with D
            RET     NZ                   ; Different - Exit
            LD      A,L                  ; Get L
            SUB     E                    ; Compare with E
            RET                          ; Return status

CHKSYN:     LD      A,(HL)               ; Check syntax of character
            EX      (SP),HL              ; Address of test byte
            CP      (HL)                 ; Same as in code string?
            INC     HL                   ; Return address
            EX      (SP),HL              ; Put it back
            JP      Z,GETCHR             ; Yes - Get next character
            JP      SNERR                ; Different - ?SN Error

OUTC:       PUSH    AF                   ; Save character
            LD      A,(CTLOFG)           ; Get control "O" flag
            OR      A                    ; Is it set?
            JP      NZ,POPAF             ; Yes - don't output
            POP     AF                   ; Restore character
            PUSH    BC                   ; Save buffer length
            PUSH    AF                   ; Save character
            CP      ' '                  ; Is it a control code?
            JP      C,DINPOS             ; Yes - Don't INC POS(X)
            LD      A,(LWIDTH)           ; Get line width
            LD      B,A                  ; To B
            LD      A,(CURPOS)           ; Get cursor position
            INC     B                    ; Width 255?
            JP      Z,INCLEN             ; Yes - No width limit
            DEC     B                    ; Restore width
            CP      B                    ; At end of line?
            CALL    Z,PRNTCRLF           ; Yes - output CRLF
INCLEN:     INC     A                    ; Move on one character
            LD      (CURPOS),A           ; Save new position
DINPOS:     IF INCLUDE_ANSITERM = 1
            LD      A,(ANSIENABLE)
            OR      A
            JR      Z,NOANSI
            POP     AF                   ; Restore character
            POP     BC                   ; Restore buffer length
            CALL    ANSITERM             ; Send it via the Ansi processor.
            RET
            ENDIF
NOANSI:     POP     AF                   ; Restore character
            POP     BC                   ; Restore buffer length
            CALL    PRNT                 ; Send it .
            RET

CLOTST:     CALL    GETKY                ; Get input character
            AND     01111111B            ; Strip bit 7
            CP      CTRL_O               ; Is it control "O"?
            RET     NZ                   ; No don't flip flag
            LD      A,(CTLOFG)           ; Get flag
            CPL                          ; Flip it
            LD      (CTLOFG),A           ; Put it back
            XOR     A                    ; Null character
            RET

LIST:       CALL    ATOH                 ; ASCII number to DE
            RET     NZ                   ; Return if anything extra
            POP     BC                   ; Rubbish - Not needed
            CALL    SRCHLN               ; Search for line number in DE
            PUSH    BC                   ; Save address of line
            CALL    SETLIN               ; Set up lines counter
LISTLP:     POP     HL                   ; Restore address of line
            LD      C,(HL)               ; Get LSB of next line
            INC     HL
            LD      B,(HL)               ; Get MSB of next line
            INC     HL
            LD      A,B                  ; BC = 0 (End of program)?
            OR      C
            JP      Z,PRNTOK             ; Yes - Go to command mode
            CALL    COUNT                ; Count lines
            CALL    TSTBRK               ; Test for break key
            PUSH    BC                   ; Save address of next line
            CALL    PRNTCRLF             ; Output CRLF
            LD      E,(HL)               ; Get LSB of line number
            INC     HL
            LD      D,(HL)               ; Get MSB of line number
            INC     HL
            PUSH    HL                   ; Save address of line start
            EX      DE,HL                ; Line number to HL
            CALL    PRNTHL               ; Output line number in decimal
            LD      A,' '                ; Space after line number
            POP     HL                   ; Restore start of line address
LSTLP2:     CALL    OUTC                 ; Output character in A
LSTLP3:     LD      A,(HL)               ; Get next byte in line
            OR      A                    ; End of line?
            INC     HL                   ; To next byte in line
            JP      Z,LISTLP             ; Yes - get next line
            JP      P,LSTLP2             ; No token - output it
            SUB     ZEND-1               ; Find and output word
            LD      C,A                  ; Token offset+1 to C
            LD      DE,WORDS             ; Reserved word list
FNDTOK:     LD      A,(DE)               ; Get character in list
            INC     DE                   ; Move on to next
            OR      A                    ; Is it start of word?
            JP      P,FNDTOK             ; No - Keep looking for word
            DEC     C                    ; Count words
            JP      NZ,FNDTOK            ; Not there - keep looking
OUTWRD:     AND     01111111B            ; Strip bit 7
            CALL    OUTC                 ; Output first character
            LD      A,(DE)               ; Get next character
            INC     DE                   ; Move on to next
            OR      A                    ; Is it end of word?
            JP      P,OUTWRD             ; No - output the rest
            JP      LSTLP3               ; Next byte in line

SETLIN:     PUSH    HL                   ; Set up LINES counter
            LD      HL,(LINESN)          ; Get LINES number
            LD      (LINESC),HL          ; Save in LINES counter
            POP     HL
            RET

COUNT:      PUSH    HL                   ; Save code string address
            PUSH    DE
            LD      HL,(LINESC)          ; Get LINES counter
            LD      DE,-1
            ADC     HL,DE                ; Decrement
            LD      (LINESC),HL          ; Put it back
            POP     DE
            POP     HL                   ; Restore code string address
            RET     P                    ; Return if more lines to go
            PUSH    HL                   ; Save code string address
            LD      HL,(LINESN)          ; Get LINES number
            LD      (LINESC),HL          ; Reset LINES counter
            CALL    GETKY                ; Get input character
            CP      CTRL_C               ; Is it control "C"?
            JP      Z,RSLNBK             ; Yes - Reset LINES and break
            POP     HL                   ; Restore code string address
            JP      COUNT                ; Keep on counting

RSLNBK:     LD      HL,(LINESN)          ; Get LINES number
            LD      (LINESC),HL          ; Reset LINES counter
            JP      BRKRET               ; Go and output "Break"

FOR:        LD      A,64H                ; Flag "FOR" assignment
            LD      (FORFLG),A           ; Save "FOR" flag
            CALL    LET                  ; Set up initial index
            POP     BC                   ; Drop RETurn address
            PUSH    HL                   ; Save code string address
            CALL    DATA                 ; Get next statement address
            LD      (LOOPST),HL          ; Save it for start of loop
            LD      HL,2                 ; Offset for "FOR" block
            ADD     HL,SP                ; Point to it
FORSLP:     CALL    LOKFOR               ; Look for existing "FOR" block
            POP     DE                   ; Get code string address
            JP      NZ,FORFND            ; No nesting found
            ADD     HL,BC                ; Move into "FOR" block
            PUSH    DE                   ; Save code string address
            DEC     HL
            LD      D,(HL)               ; Get MSB of loop statement
            DEC     HL
            LD      E,(HL)               ; Get LSB of loop statement
            INC     HL
            INC     HL
            PUSH    HL                   ; Save block address
            LD      HL,(LOOPST)          ; Get address of loop statement
            CALL    CPDEHL               ; Compare the FOR loops
            POP     HL                   ; Restore block address
            JP      NZ,FORSLP            ; Different FORs - Find another
            POP     DE                   ; Restore code string address
            LD      SP,HL                ; Remove all nested loops

FORFND:     EX      DE,HL                ; Code string address to HL
            LD      C,8
            CALL    CHKSTK               ; Check for 8 levels of stack
            PUSH    HL                   ; Save code string address
            LD      HL,(LOOPST)          ; Get first statement of loop
            EX      (SP),HL              ; Save and restore code string
            PUSH    HL                   ; Re-save code string address
            LD      HL,(LINEAT)          ; Get current line number
            EX      (SP),HL              ; Save and restore code string
            CALL    TSTNUM               ; Make sure it's a number
            CALL    CHKSYN               ; Make sure "TO" is next
            DB      ZTO                  ; "TO" token
            CALL    GETNUM               ; Get "TO" expression value
            PUSH    HL                   ; Save code string address
            CALL    BCDEFP               ; Move "TO" value to BCDE
            POP     HL                   ; Restore code string address
            PUSH    BC                   ; Save "TO" value in block
            PUSH    DE
            LD      BC,8100H             ; BCDE - 1 (default STEP)
            LD      D,C                  ; C=0
            LD      E,D                  ; D=0
            LD      A,(HL)               ; Get next byte in code string
            CP      ZSTEP                ; See if "STEP" is stated
            LD      A,1                  ; Sign of step = 1
            JP      NZ,SAVSTP            ; No STEP given - Default to 1
            CALL    GETCHR               ; Jump over "STEP" token
            CALL    GETNUM               ; Get step value
            PUSH    HL                   ; Save code string address
            CALL    BCDEFP               ; Move STEP to BCDE
            CALL    TSTSGN               ; Test sign of FPREG
            POP     HL                   ; Restore code string address
SAVSTP:     PUSH    BC                   ; Save the STEP value in block
            PUSH    DE
            PUSH    AF                   ; Save sign of STEP
            INC     SP                   ; Don't save flags
            PUSH    HL                   ; Save code string address
            LD      HL,(BRKLIN)          ; Get address of index variable
            EX      (SP),HL              ; Save and restore code string
PUTFID:     LD      B,ZFOR               ; "FOR" block marker
            PUSH    BC                   ; Save it
            INC     SP                   ; Don't save C

RUNCNT:     CALL    TSTBRK               ; Execution driver - Test break
            LD      (BRKLIN),HL          ; Save code address for break
            LD      A,(HL)               ; Get next byte in code string
            CP      ':'                  ; Multi statement line?
            JP      Z,EXCUTE             ; Yes - Execute it
            OR      A                    ; End of line?
            JP      NZ,SNERR             ; No - Syntax error
            INC     HL                   ; Point to address of next line
            LD      A,(HL)               ; Get LSB of line pointer
            INC     HL
            OR      (HL)                 ; Is it zero (End of prog)?
            JP      Z,ENDPRG             ; Yes - Terminate execution
            INC     HL                   ; Point to line number
            LD      E,(HL)               ; Get LSB of line number
            INC     HL
            LD      D,(HL)               ; Get MSB of line number
            EX      DE,HL                ; Line number to HL
            LD      (LINEAT),HL          ; Save as current line number
            EX      DE,HL                ; Line number back to DE
EXCUTE:     CALL    GETCHR               ; Get key word
            LD      DE,RUNCNT            ; Where to RETurn to
            PUSH    DE                   ; Save for RETurn
IFJMP:      RET     Z                    ; Go to RUNCNT if end of STMT
ONJMP:      SUB     ZEND                 ; Is it a token?
            JP      C,LET                ; No - try to assign it
            CP      ZNEW+1-ZEND          ; END to NEW ?
            JP      NC,SNERR             ; Not a key word - ?SN Error
            RLCA                         ; Double it
            LD      C,A                  ; BC = Offset into table
            LD      B,0
            EX      DE,HL                ; Save code string address
            LD      HL,WORDTB            ; Keyword address table
            ADD     HL,BC                ; Point to routine address
            LD      C,(HL)               ; Get LSB of routine address
            INC     HL
            LD      B,(HL)               ; Get MSB of routine address
            PUSH    BC                   ; Save routine address
            EX      DE,HL                ; Restore code string address

GETCHR:     INC     HL                   ; Point to next character
            LD      A,(HL)               ; Get next code string byte
            CP      ':'                  ; Z if ':'
            RET     NC                   ; NC if > "9"
            CP      ' '
            JP      Z,GETCHR             ; Skip over spaces
            CP      '0'
            CCF                          ; NC if < '0'
            INC     A                    ; Test for zero - Leave carry
            DEC     A                    ; Z if Null
            RET

RESTOR:     EX      DE,HL                ; Save code string address
            LD      HL,(BASTXT)          ; Point to start of program
            JP      Z,RESTNL             ; Just RESTORE - reset pointer
            EX      DE,HL                ; Restore code string address
            CALL    ATOH                 ; Get line number to DE
            PUSH    HL                   ; Save code string address
            CALL    SRCHLN               ; Search for line number in DE
            LD      H,B                  ; HL = Address of line
            LD      L,C
            POP     DE                   ; Restore code string address
            JP      NC,ULERR             ; ?UL Error if not found
RESTNL:     DEC     HL                   ; Byte before DATA statement
UPDATA:     LD      (NXTDAT),HL          ; Update DATA pointer
            EX      DE,HL                ; Restore code string address
            RET

TSTBRK:     CALL    CHKKY                ; Check input status
            OR      A
            RET     Z                    ; No key, go back
            CALL    GETKY                ; Get the key into A
            CP      ESC                  ; Escape key?
            JR      Z,BRK                ; Yes, break
            CP      CTRL_C               ; <Ctrl-C>
            JR      Z,BRK                ; Yes, break
            CP      CTRL_S               ; Stop scrolling?
            RET     NZ                   ; Other key, ignore


STALL:      CALL    GETKY                ; Wait for key
            CP      CTRL_Q               ; Resume scrolling?
            RET      Z                   ; Release the chokehold
            CP      CTRL_C               ; Second break?
            JR      Z,STOP               ; Break during hold exits prog
            JR      STALL                ; Loop until <Ctrl-Q> or <brk>

BRK         LD      A,0FFH               ; Set BRKFLG
            LD      (BRKFLG),A           ; Store it


STOP:       RET     NZ                   ; Exit if anything else
            DB      0F6H                 ; Flag "STOP"
PEND:       RET     NZ                   ; Exit if anything else
            LD      (BRKLIN),HL          ; Save point of break
            DB      21H                  ; Skip "OR 11111111B"
INPBRK:     OR      11111111B            ; Flag "Break" wanted
            POP     BC                   ; Return not needed and more
ENDPRG:     LD      HL,(LINEAT)          ; Get current line number
            PUSH    AF                   ; Save STOP / END status
            LD      A,L                  ; Is it direct break?
            AND     H
            INC     A                    ; Line is -1 if direct break
            JP      Z,NOLIN              ; Yes - No line number
            LD      (ERRLIN),HL          ; Save line of break
            LD      HL,(BRKLIN)          ; Get point of break
            LD      (CONTAD),HL          ; Save point to CONTinue
NOLIN:      XOR     A
            LD      (CTLOFG),A           ; Enable output
            CALL    STTLIN               ; Start a new line
            POP     AF                   ; Restore STOP / END status
            LD      HL,BRKMSG            ; "Break" message
            JP      NZ,ERRIN             ; "in line" wanted?
            JP      PRNTOK               ; Go to command mode

CONT:       LD      HL,(CONTAD)          ; Get CONTinue address
            LD      A,H                  ; Is it zero?
            OR      L
            LD      E,CN                 ; ?CN Error
            JP      Z,BERROR             ; Yes - output "?CN Error"
            EX      DE,HL                ; Save code string address
            LD      HL,(ERRLIN)          ; Get line of last break
            LD      (LINEAT),HL          ; Set up current line number
            EX      DE,HL                ; Restore code string address
            RET                          ; CONTinue where left off

NULL:       CALL    GETINT               ; Get integer 0-255
            RET     NZ                   ; Return if bad value
            LD      (NULLS),A            ; Set nulls number
            RET


ACCSUM:     PUSH    HL                   ; Save address in array
            LD      HL,(CHKSUM)          ; Get check sum
            LD      B,0                  ; BC - Value of byte
            LD      C,A
            ADD     HL,BC                ; Add byte to check sum
            LD      (CHKSUM),HL          ; Re-save check sum
            POP     HL                   ; Restore address in array
            RET

CHKLTR:     LD      A,(HL)               ; Get byte
            CP      'A'                  ; < 'a' ?
            RET     C                    ; Carry set if not letter
            CP      'Z'+1                ; > 'z' ?
            CCF
            RET                          ; Carry set if not letter

FPSINT:     CALL    GETCHR               ; Get next character
POSINT:     CALL    GETNUM               ; Get integer 0 to 32767
DEPINT:     CALL    TSTSGN               ; Test sign of FPREG
            JP      M,FCERR              ; Negative - ?FC Error
DEINT:      LD      A,(FPEXP)            ; Get integer value to DE
            CP      80H+16               ; Exponent in range (16 bits)?
            JP      C,FPINT              ; Yes - convert it
            LD      BC,9080H             ; BCDE = -32768
            LD      DE,0000
            PUSH    HL                   ; Save code string address
            CALL    CMPNUM               ; Compare FPREG with BCDE
            POP     HL                   ; Restore code string address
            LD      D,C                  ; MSB to D
            RET     Z                    ; Return if in range
FCERR:      LD      E,FC                 ; ?FC Error
            JP      BERROR               ; Output error-

ATOH:       DEC     HL                   ; ASCII number to DE binary
GETLN:      LD      DE,0                 ; Get number to DE
GTLNLP:     CALL    GETCHR               ; Get next character
            RET     NC                   ; Exit if not a digit
            PUSH    HL                   ; Save code string address
            PUSH    AF                   ; Save digit
            LD      HL,65529/10          ; Largest number 65529
            CALL    CPDEHL               ; Number in range?
            JP      C,SNERR              ; No - ?SN Error
            LD      H,D                  ; HL = Number
            LD      L,E
            ADD     HL,DE                ; Times 2
            ADD     HL,HL                ; Times 4
            ADD     HL,DE                ; Times 5
            ADD     HL,HL                ; Times 10
            POP     AF                   ; Restore digit
            SUB     '0'                  ; Make it 0 to 9
            LD      E,A                  ; DE = Value of digit
            LD      D,0
            ADD     HL,DE                ; Add to number
            EX      DE,HL                ; Number to DE
            POP     HL                   ; Restore code string address
            JP      GTLNLP               ; Go to next character

CLEAR:      JP      Z,INTVAR             ; Just "CLEAR" Keep parameters
            CALL    POSINT               ; Get integer 0 to 32767 to DE
            DEC     HL                   ; Cancel increment
            CALL    GETCHR               ; Get next character
            PUSH    HL                   ; Save code string address
            LD      HL,(LSTRAM)          ; Get end of RAM
            JP      Z,STORED             ; No value given - Use stored
            POP     HL                   ; Restore code string address
            CALL    CHKSYN               ; Check for comma
            DB         ','
            PUSH    DE                   ; Save number
            CALL    POSINT               ; Get integer 0 to 32767
            DEC     HL                   ; Cancel increment
            CALL    GETCHR               ; Get next character
            JP      NZ,SNERR             ; ?SN Error if more on line
            EX      (SP),HL              ; Save code string address
            EX      DE,HL                ; Number to DE
STORED:     LD      A,L                  ; Get LSB of new RAM top
            SUB     E                    ; Subtract LSB of string space
            LD      E,A                  ; Save LSB
            LD      A,H                  ; Get MSB of new RAM top
            SBC     A,D                  ; Subtract MSB of string space
            LD      D,A                  ; Save MSB
            JP      C,OMERR              ; ?OM Error if not enough mem
            PUSH    HL                   ; Save RAM top
            LD      HL,(PROGND)          ; Get program end
            LD      BC,40                ; 40 Bytes minimum working RAM
            ADD     HL,BC                ; Get lowest address
            CALL    CPDEHL               ; Enough memory?
            JP      NC,OMERR             ; No - ?OM Error
            EX      DE,HL                ; RAM top to HL
            LD      (STRSPC),HL          ; Set new string space
            POP     HL                   ; End of memory to use
            LD      (LSTRAM),HL          ; Set new top of RAM
            POP     HL                   ; Restore code string address
            JP      INTVAR               ; Initialise variables

RUN:        JP      Z,RUNFST             ; RUN from start if just RUN
            CALL    INTVAR               ; Initialise variables
            LD      BC,RUNCNT            ; Execution driver loop
            JP      RUNLIN               ; RUN from line number

GOSUB:      LD      C,3                  ; 3 Levels of stack needed
            CALL    CHKSTK               ; Check for 3 levels of stack
            POP     BC                   ; Get return address
            PUSH    HL                   ; Save code string for RETURN
            PUSH    HL                   ; And for GOSUB routine
            LD      HL,(LINEAT)          ; Get current line
            EX      (SP),HL              ; Into stack - Code string out
            LD      A,ZGOSUB             ; "GOSUB" token
            PUSH    AF                   ; Save token
            INC     SP                   ; Don't save flags

RUNLIN:     PUSH    BC                   ; Save return address
GOTO:       CALL    ATOH                 ; ASCII number to DE binary
            CALL    REM                  ; Get end of line
            PUSH    HL                   ; Save end of line
            LD      HL,(LINEAT)          ; Get current line
            CALL    CPDEHL               ; Line after current?
            POP     HL                   ; Restore end of line
            INC     HL                   ; Start of next line
            CALL    C,SRCHLP             ; Line is after current line
            CALL    NC,SRCHLN            ; Line is before current line
            LD      H,B                  ; Set up code string address
            LD      L,C
            DEC     HL                   ; Incremented after
            RET     C                    ; Line found
ULERR:      LD      E,UL                 ; ?UL Error
            JP      BERROR               ; Output error message

RETURN:     RET     NZ                   ; Return if not just RETURN
            LD      D,-1                 ; Flag "GOSUB" search
            CALL    BAKSTK               ; Look "GOSUB" block
            LD      SP,HL                ; Kill all FORs in subroutine
            CP      ZGOSUB               ; Test for "GOSUB" token
            LD      E,RG                 ; ?RG Error
            JP      NZ,BERROR            ; Error if no "GOSUB" found
            POP     HL                   ; Get RETURN line number
            LD      (LINEAT),HL          ; Save as current
            INC     HL                   ; Was it from direct statement?
            LD      A,H
            OR      L                    ; Return to line
            JP      NZ,RETLIN            ; No - Return to line
            LD      A,(LSTBIN)           ; Any INPUT in subroutine?
            OR      A                    ; If so buffer is corrupted
            JP      NZ,POPNOK            ; Yes - Go to command mode
RETLIN:     LD      HL,RUNCNT            ; Execution driver loop
            EX      (SP),HL              ; Into stack - Code string out
            DB         3EH                  ; Skip "POP HL"
NXTDTA:     POP     HL                   ; Restore code string address

DATA:       DB      01H,3AH              ; ':' End of statement
REM:        LD      C,0                  ; 00  End of statement
            LD      B,0
NXTSTL:     LD      A,C                  ; Statement and byte
            LD      C,B
            LD      B,A                  ; Statement end byte
NXTSTT:     LD      A,(HL)               ; Get byte
            OR      A                    ; End of line?
            RET     Z                    ; Yes - Exit
            CP      B                    ; End of statement?
            RET     Z                    ; Yes - Exit
            INC     HL                   ; Next byte
            CP      '"'                  ; Literal string?
            JP      Z,NXTSTL             ; Yes - Look for another '"'
            JP      NXTSTT               ; Keep looking

LET:        CALL    GETVAR               ; Get variable name
            CALL    CHKSYN               ; Make sure "=" follows
            DB         ZEQUAL               ; "=" token
            PUSH    DE                   ; Save address of variable
            LD      A,(TYPE)             ; Get data type
            PUSH    AF                   ; Save type
            CALL    EVAL                 ; Evaluate expression
            POP     AF                   ; Restore type
            EX      (SP),HL              ; Save code - Get var addr
            LD      (BRKLIN),HL          ; Save address of variable
            RRA                          ; Adjust type
            CALL    CHKTYP               ; Check types are the same
            JP      Z,LETNUM             ; Numeric - Move value
LETSTR:     PUSH    HL                   ; Save address of string var
            LD      HL,(FPREG)           ; Pointer to string entry
            PUSH    HL                   ; Save it on stack
            INC     HL                   ; Skip over length
            INC     HL
            LD      E,(HL)               ; LSB of string address
            INC     HL
            LD      D,(HL)               ; MSB of string address
            LD      HL,(BASTXT)          ; Point to start of program
            CALL    CPDEHL               ; Is string before program?
            JP      NC,CRESTR            ; Yes - Create string entry
            LD      HL,(STRSPC)          ; Point to string space
            CALL    CPDEHL               ; Is string literal in program?
            POP     DE                   ; Restore address of string
            JP      NC,MVSTPT            ; Yes - Set up pointer
            LD      HL,TMPSTR            ; Temporary string pool
            CALL    CPDEHL               ; Is string in temporary pool?
            JP      NC,MVSTPT            ; No - Set up pointer
            DB      3EH                  ; Skip "POP DE"
CRESTR:     POP     DE                   ; Restore address of string
            CALL    BAKTMP               ; Back to last tmp-str entry
            EX      DE,HL                ; Address of string entry
            CALL    SAVSTR               ; Save string in string area
MVSTPT:     CALL    BAKTMP               ; Back to last tmp-str entry
            POP     HL                   ; Get string pointer
            CALL    DETHL4               ; Move string pointer to var
            POP     HL                   ; Restore code string address
            RET

LETNUM:     PUSH    HL                   ; Save address of variable
            CALL    FPTHL                ; Move value to variable
            POP     DE                   ; Restore address of variable
            POP     HL                   ; Restore code string address
            RET

ON:         CALL    GETINT               ; Get integer 0-255
            LD      A,(HL)               ; Get "GOTO" or "GOSUB" token
            LD      B,A                  ; Save in B
            CP      ZGOSUB               ; "GOSUB" token?
            JP      Z,ONGO               ; Yes - Find line number
            CALL    CHKSYN               ; Make sure it's "GOTO"
            DB      ZGOTO                ; "GOTO" token
            DEC     HL                   ; Cancel increment
ONGO:       LD      C,E                  ; Integer of branch value
ONGOLP:     DEC     C                    ; Count branches
            LD      A,B                  ; Get "GOTO" or "GOSUB" token
            JP      Z,ONJMP              ; Go to that line if right one
            CALL    GETLN                ; Get line number to DE
            CP      ','                  ; Another line number?
            RET     NZ                   ; No - Drop through
            JP      ONGOLP               ; Yes - loop

IF:         CALL    EVAL                 ; Evaluate expression
            LD      A,(HL)               ; Get token
            CP      ZGOTO                ; "GOTO" token?
            JP      Z,IFGO               ; Yes - Get line
            CALL    CHKSYN               ; Make sure it's "THEN"
            DB         ZTHEN                ; "THEN" token
            DEC     HL                   ; Cancel increment
IFGO:       CALL    TSTNUM               ; Make sure it's numeric
            CALL    TSTSGN               ; Test state of expression
            JP      Z,REM                ; False - Drop through
            CALL    GETCHR               ; Get next character
            JP      C,GOTO               ; Number - GOTO that line
            JP      IFJMP                ; Otherwise do statement

MRPRNT:     DEC     HL                   ; DEC 'cos GETCHR INCs
            CALL    GETCHR               ; Get next character
PRINT:      JP      Z,PRNTCRLF           ; CRLF if just PRINT
PRNTLP:     RET     Z                    ; End of list - Exit
            CP      ZTAB                 ; "TAB(" token?
            JP      Z,DOTAB              ; Yes - Do TAB routine
            CP      ZSPC                 ; "SPC(" token?
            JP      Z,DOTAB              ; Yes - Do SPC routine
            PUSH    HL                   ; Save code string address
            CP      ','                  ; Comma?
            JP      Z,DOCOM              ; Yes - Move to next zone
            CP      59 ;";"              ; Semi-colon?
            JP      Z,NEXITM             ; Do semi-colon routine
            POP     BC                   ; Code string address to BC
            CALL    EVAL                 ; Evaluate expression
            PUSH    HL                   ; Save code string address
            LD      A,(TYPE)             ; Get variable type
            OR      A                    ; Is it a string variable?
            JP      NZ,PRNTST            ; Yes - Output string contents
            CALL    NUMASC               ; Convert number to text
            CALL    CRTST                ; Create temporary string
            LD      (HL),' '             ; Followed by a space
            LD      HL,(FPREG)           ; Get length of output
            INC     (HL)                 ; Plus 1 for the space
            LD      HL,(FPREG)           ; < Not needed >
            LD      A,(LWIDTH)           ; Get width of line
            LD      B,A                  ; To B
            INC     B                    ; Width 255 (No limit)?
            JP      Z,PRNTNB             ; Yes - Output number string
            INC     B                    ; Adjust it
            LD      A,(CURPOS)           ; Get cursor position
            ADD     A,(HL)               ; Add length of string
            DEC     A                    ; Adjust it
            CP      B                    ; Will output fit on this line?
            CALL    NC,PRNTCRLF          ; No - CRLF first
PRNTNB:     CALL    PRS1                 ; Output string at (HL)
            XOR     A                    ; Skip CALL by setting 'z' flag
PRNTST:     CALL    NZ,PRS1              ; Output string at (HL)
            POP     HL                   ; Restore code string address
            JP      MRPRNT               ; See if more to PRINT

STTLIN:     LD      A,(CURPOS)           ; Make sure on new line
            OR      A                    ; Already at start?
            RET     Z                    ; Yes - Do nothing
            JP      PRNTCRLF             ; Start a new line

ENDINP:     LD      (HL),0               ; Mark end of buffer
            LD      HL,BUFFER-1          ; Point to buffer
PRNTCRLF:   LD     A,CR                 ; Load a CR
            CALL    OUTC                 ; Output character
            LD      A,LF                 ; Load a LF
            CALL    OUTC                 ; Output character
DONULL:     XOR     A                    ; Set to position 0
            LD      (CURPOS),A           ; Store it
            LD      A,(NULLS)            ; Get number of nulls
NULLP:      DEC     A                    ; Count them
            RET     Z                    ; Return if done
            PUSH    AF                   ; Save count
            XOR     A                    ; Load a null
            CALL    OUTC                 ; Output it
            POP     AF                   ; Restore count
            JP      NULLP                ; Keep counting

DOCOM:      LD      A,(COMMAN)           ; Get comma width
            LD      B,A                  ; Save in B
            LD      A,(CURPOS)           ; Get current position
            CP      B                    ; Within the limit?
            CALL    NC,PRNTCRLF          ; No - output CRLF
            JP      NC,NEXITM            ; Get next item
ZONELP:     SUB     14                   ; Next zone of 14 characters
            JP      NC,ZONELP            ; Repeat if more zones
            CPL                          ; Number of spaces to output
            JP      ASPCS                ; Output them

DOTAB:      PUSH    AF                   ; Save token
            CALL    FNDNUM               ; Evaluate expression
            CALL    CHKSYN               ; Make sure ")" follows
            DB      ")"
            DEC     HL                   ; Back space on to ")"
            POP     AF                   ; Restore token
            SUB     ZSPC                 ; Was it "SPC(" ?
            PUSH    HL                   ; Save code string address
            JP      Z,DOSPC              ; Yes - Do 'E' spaces
            LD      A,(CURPOS)           ; Get current position
DOSPC:      CPL                          ; Number of spaces to print to
            ADD     A,E                  ; Total number to print
            JP      NC,NEXITM            ; TAB < Current POS(X)
ASPCS:      INC     A                    ; Output A spaces
            LD      B,A                  ; Save number to print
            LD      A,' '                ; Space
SPCLP:      CALL    OUTC                 ; Output character in A
            DEC     B                    ; Count them
            JP      NZ,SPCLP             ; Repeat if more
NEXITM:     POP     HL                   ; Restore code string address
            CALL    GETCHR               ; Get next character
            JP      PRNTLP               ; More to print

REDO:       DB      "?Redo from start",CR,LF,0

BADINP:     LD      A,(READFG)           ; READ or INPUT?
            OR      A
            JP      NZ,DATSNR            ; READ - ?SN Error
            POP     BC                   ; Throw away code string addr
            LD      HL,REDO              ; "Redo from start" message
            CALL    PRS                  ; Output string
            JP      DOAGN                ; Do last INPUT again

INPUT:      CALL    IDTEST               ; Test for illegal direct
            LD      A,(HL)               ; Get character after "INPUT"
            CP      '"'                  ; Is there a prompt string?
            LD      A,0                  ; Clear A and leave flags
            LD      (CTLOFG),A           ; Enable output
            JP      NZ,NOPMPT            ; No prompt - get input
            CALL    QTSTR                ; Get string terminated by '"'
            CALL    CHKSYN               ; Check for ';' after prompt
            DB      ';'
            PUSH    HL                   ; Save code string address
            CALL    PRS1                 ; Output prompt string
            DB      3EH                  ; Skip "PUSH HL"
NOPMPT:     PUSH    HL                   ; Save code string address
            CALL    PROMPT               ; Get input with "? " prompt
            POP     BC                   ; Restore code string address
            JP      C,INPBRK             ; Break pressed - Exit
            INC     HL                   ; Next byte
            LD      A,(HL)               ; Get it
            OR      A                    ; End of line?
            DEC     HL                   ; Back again
            PUSH    BC                   ; Re-save code string address
            JP      Z,NXTDTA             ; Yes - Find next DATA stmt
            LD      (HL),','             ; Store comma as separator
            JP      NXTITM               ; Get next item

READ:       PUSH    HL                   ; Save code string address
            LD      HL,(NXTDAT)          ; Next DATA statement
            DB      0F6H                 ; Flag "READ"
NXTITM:     XOR     A                    ; Flag "INPUT"
            LD      (READFG),A           ; Save "READ"/"INPUT" flag
            EX      (SP),HL              ; Get code str' , Save pointer
            JP      GTVLUS               ; Get values

NEDMOR:     CALL    CHKSYN               ; Check for comma between items
            DB         ','
GTVLUS:     CALL    GETVAR               ; Get variable name
            EX      (SP),HL              ; Save code str" , Get pointer
            PUSH    DE                   ; Save variable address
            LD      A,(HL)               ; Get next "INPUT"/"DATA" byte
            CP      ','                  ; Comma?
            JP      Z,ANTVLU             ; Yes - Get another value
            LD      A,(READFG)           ; Is it READ?
            OR      A
            JP      NZ,FDTLP             ; Yes - Find next DATA stmt
            LD      A,'?'                ; More INPUT needed
            CALL    OUTC                 ; Output character
            CALL    PROMPT               ; Get INPUT with prompt
            POP     DE                   ; Variable address
            POP     BC                   ; Code string address
            JP      C,INPBRK             ; Break pressed
            INC     HL                   ; Point to next DATA byte
            LD      A,(HL)               ; Get byte
            OR      A                    ; Is it zero (No input) ?
            DEC     HL                   ; Back space INPUT pointer
            PUSH    BC                   ; Save code string address
            JP      Z,NXTDTA             ; Find end of buffer
            PUSH    DE                   ; Save variable address
ANTVLU:     LD      A,(TYPE)             ; Check data type
            OR      A                    ; Is it numeric?
            JP      Z,INPBIN             ; Yes - Convert to binary
            CALL    GETCHR               ; Get next character
            LD      D,A                  ; Save input character
            LD      B,A                  ; Again
            CP      '"'                  ; Start of literal sting?
            JP      Z,STRENT             ; Yes - Create string entry
            LD      A,(READFG)           ; "READ" or "INPUT" ?
            OR      A
            LD      D,A                  ; Save 00 if "INPUT"
            JP      Z,ITMSEP             ; "INPUT" - End with 00
            LD      D,':'                ; "DATA" - End with 00 or ':'
ITMSEP:     LD      B,','                ; Item separator
            DEC     HL                   ; Back space for DTSTR
STRENT:     CALL    DTSTR                ; Get string terminated by D
            EX      DE,HL                ; String address to DE
            LD      HL,LTSTND            ; Where to go after LETSTR
            EX      (SP),HL              ; Save HL , get input pointer
            PUSH    DE                   ; Save address of string
            JP      LETSTR               ; Assign string to variable

INPBIN:     CALL    GETCHR               ; Get next character
            CALL    ASCTFP               ; Convert ASCII to FP number
            EX      (SP),HL              ; Save input ptr, Get var addr
            CALL    FPTHL                ; Move FPREG to variable
            POP     HL                   ; Restore input pointer
LTSTND:     DEC     HL                   ; DEC 'cos GETCHR INCs
            CALL    GETCHR               ; Get next character
            JP      Z,MORDT              ; End of line - More needed?
            CP      ','                  ; Another value?
            JP      NZ,BADINP            ; No - Bad input
MORDT:      EX      (SP),HL              ; Get code string address
            DEC     HL                   ; DEC 'cos GETCHR INCs
            CALL    GETCHR               ; Get next character
            JP      NZ,NEDMOR            ; More needed - Get it
            POP     DE                   ; Restore DATA pointer
            LD      A,(READFG)           ; "READ" or "INPUT" ?
            OR      A
            EX      DE,HL                ; DATA pointer to HL
            JP      NZ,UPDATA            ; Update DATA pointer if "READ"
            PUSH    DE                   ; Save code string address
            OR      (HL)                 ; More input given?
            LD      HL,EXTIG             ; "?Extra ignored" message
            CALL    NZ,PRS               ; Output string if extra given
            POP     HL                   ; Restore code string address
            RET

EXTIG:      DB      "?Extra ignored",CR,LF,0

FDTLP:      CALL    DATA                 ; Get next statement
            OR      A                    ; End of line?
            JP      NZ,FANDT             ; No - See if DATA statement
            INC     HL
            LD      A,(HL)               ; End of program?
            INC     HL
            OR      (HL)                 ; 00 00 Ends program
            LD      E,OD                 ; ?OD Error
            JP      Z,BERROR             ; Yes - Out of DATA
            INC     HL
            LD      E,(HL)               ; LSB of line number
            INC     HL
            LD      D,(HL)               ; MSB of line number
            EX      DE,HL
            LD      (DATLIN),HL          ; Set line of current DATA item
            EX      DE,HL
FANDT:      CALL    GETCHR               ; Get next character
            CP      ZDATA                ; "DATA" token
            JP      NZ,FDTLP             ; No "DATA" - Keep looking
            JP      ANTVLU               ; Found - Convert input

NEXT:       LD      DE,0                 ; In case no index given
NEXT1:      CALL    NZ,GETVAR            ; Get index address
            LD      (BRKLIN),HL          ; Save code string address
            CALL    BAKSTK               ; Look for "FOR" block
            JP      NZ,NFERR             ; No "FOR" - ?NF Error
            LD      SP,HL                ; Clear nested loops
            PUSH    DE                   ; Save index address
            LD      A,(HL)               ; Get sign of STEP
            INC     HL
            PUSH    AF                   ; Save sign of STEP
            PUSH    DE                   ; Save index address
            CALL    PHLTFP               ; Move index value to FPREG
            EX      (SP),HL              ; Save address of TO value
            PUSH    HL                   ; Save address of index
            CALL    ADDPHL               ; Add STEP to index value
            POP     HL                   ; Restore address of index
            CALL    FPTHL                ; Move value to index variable
            POP     HL                   ; Restore address of TO value
            CALL    LOADFP               ; Move TO value to BCDE
            PUSH    HL                   ; Save address of line of FOR
            CALL    CMPNUM               ; Compare index with TO value
            POP     HL                   ; Restore address of line num
            POP     BC                   ; Address of sign of STEP
            SUB     B                    ; Compare with expected sign
            CALL    LOADFP               ; BC = Loop stmt,DE = Line num
            JP      Z,KILFOR             ; Loop finished - Terminate it
            EX      DE,HL                ; Loop statement line number
            LD      (LINEAT),HL          ; Set loop line number
            LD      L,C                  ; Set code string to loop
            LD      H,B
            JP      PUTFID               ; Put back "FOR" and continue

KILFOR:     LD      SP,HL                ; Remove "FOR" block
            LD      HL,(BRKLIN)          ; Code string after "NEXT"
            LD      A,(HL)               ; Get next byte in code string
            CP      ','                  ; More NEXTs ?
            JP      NZ,RUNCNT            ; No - Do next statement
            CALL    GETCHR               ; Position to index name
            CALL    NEXT1                ; Re-enter NEXT routine
        ; < will not RETurn to here , Exit to RUNCNT or Loop >

GETNUM:     CALL    EVAL                 ; Get a numeric expression
TSTNUM:     DB      0F6H                 ; Clear carry (numeric)
TSTSTR:     SCF                          ; Set carry (string)
CHKTYP:     LD      A,(TYPE)             ; Check types match
            ADC     A,A                  ; Expected + actual
            OR      A                    ; Clear carry , set parity
            RET     PE                   ; Even parity - Types match
            JP      TMERR                ; Different types - Error

OPNPAR:     CALL    CHKSYN               ; Make sure "(" follows
            DB      "("
EVAL:       DEC     HL                   ; Evaluate expression & save
            LD      D,0                  ; Precedence value
EVAL1:      PUSH    DE                   ; Save precedence
            LD      C,1
            CALL    CHKSTK               ; Check for 1 level of stack
            CALL    OPRND                ; Get next expression value
EVAL2:      LD      (NXTOPR),HL          ; Save address of next operator
EVAL3:      LD      HL,(NXTOPR)          ; Restore address of next opr
            POP     BC                   ; Precedence value and operator
            LD      A,B                  ; Get precedence value
            CP      78H                  ; "AND" or "OR" ?
            CALL    NC,TSTNUM            ; No - Make sure it's a number
            LD      A,(HL)               ; Get next operator / function
            LD      D,0                  ; Clear Last relation
RLTLP:      SUB     ZGTR                 ; ">" Token
            JP      C,FOPRND             ; + - * / ^ AND OR - Test it
            CP      ZLTH+1-ZGTR          ; < = >
            JP      NC,FOPRND            ; Function - Call it
            CP      ZEQUAL-ZGTR          ; "="
            RLA                          ; <- Test for legal
            XOR     D                    ; <- combinations of < = >
            CP      D                    ; <- by combining last token
            LD      D,A                  ; <- with current one
            JP      C,SNERR              ; Error if "<<' '==" or ">>"
            LD      (CUROPR),HL          ; Save address of current token
            CALL    GETCHR               ; Get next character
            JP      RLTLP                ; Treat the two as one

FOPRND:     LD      A,D                  ; < = > found ?
            OR      A
            JP      NZ,TSTRED            ; Yes - Test for reduction
            LD      A,(HL)               ; Get operator token
            LD      (CUROPR),HL          ; Save operator address
            SUB     ZPLUS                ; Operator or function?
            RET     C                    ; Neither - Exit
            CP      ZOR+1-ZPLUS          ; Is it + - * / ^ AND OR ?
            RET     NC                   ; No - Exit
            LD      E,A                  ; Coded operator
            LD      A,(TYPE)             ; Get data type
            DEC     A                    ; FF = numeric , 00 = string
            OR      E                    ; Combine with coded operator
            LD      A,E                  ; Get coded operator
            JP      Z,CONCAT             ; String concatenation
            RLCA                         ; Times 2
            ADD     A,E                  ; Times 3
            LD      E,A                  ; To DE (D is 0)
            LD      HL,PRITAB            ; Precedence table
            ADD     HL,DE                ; To the operator concerned
            LD      A,B                  ; Last operator precedence
            LD      D,(HL)               ; Get evaluation precedence
            CP      D                    ; Compare with eval precedence
            RET     NC                   ; Exit if higher precedence
            INC     HL                   ; Point to routine address
            CALL    TSTNUM               ; Make sure it's a number

STKTHS:     PUSH    BC                   ; Save last precedence & token
            LD      BC,EVAL3             ; Where to go on prec' break
            PUSH    BC                   ; Save on stack for return
            LD      B,E                  ; Save operator
            LD      C,D                  ; Save precedence
            CALL    STAKFP               ; Move value to stack
            LD      E,B                  ; Restore operator
            LD      D,C                  ; Restore precedence
            LD      C,(HL)               ; Get LSB of routine address
            INC     HL
            LD      B,(HL)               ; Get MSB of routine address
            INC     HL
            PUSH    BC                   ; Save routine address
            LD      HL,(CUROPR)          ; Address of current operator
            JP      EVAL1                ; Loop until prec' break

OPRND:      XOR     A                    ; Get operand routine
            LD      (TYPE),A             ; Set numeric expected
            CALL    GETCHR               ; Get next character
            LD      E,MO                 ; ?MO Error
            JP      Z,BERROR             ; No operand - Error
            JP      C,ASCTFP             ; Number - Get value
            CALL    CHKLTR               ; See if a letter
            JP      NC,CONVAR            ; Letter - Find variable
            CP      '&'                  ; &H = HEX, &B = BINARY [G. Searle]
            JR      NZ, NOTAMP
            CALL    GETCHR               ; Get next character
            CP      'H'                  ; Hex number indicated? [function added]
            JP      Z,HEXTFP             ; Convert Hex to FPREG
            CP      'B'                  ; Binary number indicated? [function added]
            JP      Z,BINTFP             ; Convert Bin to FPREG
            LD      E,SN                 ; If neither then a ?SN Error
            JP      Z,BERROR             ; 
NOTAMP:     CP      ZPLUS                ; '+' Token ?
            JP      Z,OPRND              ; Yes - Look for operand
            CP      '.'                  ; '.' ?
            JP      Z,ASCTFP             ; Yes - Create FP number
            CP      ZMINUS               ; '-' Token ?
            JP      Z,MINUS              ; Yes - Do minus
            CP      '"'                  ; Literal string ?
            JP      Z,QTSTR              ; Get string terminated by '"'
            CP      ZNOT                 ; "NOT" Token ?
            JP      Z,EVNOT              ; Yes - Eval NOT expression
            CP      ZFN                  ; "FN" Token ?
            JP      Z,DOFN               ; Yes - Do FN routine
            SUB     ZSGN                 ; Is it a function?
            JP      NC,FNOFST            ; Yes - Evaluate function
EVLPAR:     CALL    OPNPAR               ; Evaluate expression in "()"
            CALL    CHKSYN               ; Make sure ")" follows
            DB      ")"
            RET

MINUS:      LD      D,7DH                ; '-' precedence
            CALL    EVAL1                ; Evaluate until prec' break
            LD      HL,(NXTOPR)          ; Get next operator address
            PUSH    HL                   ; Save next operator address
            CALL    INVSGN               ; Negate value
RETNUM:     CALL    TSTNUM               ; Make sure it's a number
            POP     HL                   ; Restore next operator address
            RET

CONVAR:     CALL    GETVAR               ; Get variable address to DE
FRMEVL:     PUSH    HL                   ; Save code string address
            EX      DE,HL                ; Variable address to HL
            LD      (FPREG),HL           ; Save address of variable
            LD      A,(TYPE)             ; Get type
            OR      A                    ; Numeric?
            CALL    Z,PHLTFP             ; Yes - Move contents to FPREG
            POP     HL                   ; Restore code string address
            RET

FNOFST:     LD      B,0                  ; Get address of function
            RLCA                         ; Double function offset
            LD      C,A                  ; BC = Offset in function table
            PUSH    BC                   ; Save adjusted token value
            CALL    GETCHR               ; Get next character
            LD      A,C                  ; Get adjusted token value
            CP      2*(ZLEFT-ZSGN)-1     ; Adj' LEFT$,RIGHT$ or MID$ ?
            JP      C,FNVAL              ; No - Do function
            CALL    OPNPAR               ; Evaluate expression  (X,...
            CALL    CHKSYN               ; Make sure ',' follows
            DB         ','
            CALL    TSTSTR               ; Make sure it's a string
            EX      DE,HL                ; Save code string address
            LD      HL,(FPREG)           ; Get address of string
            EX      (SP),HL              ; Save address of string
            PUSH    HL                   ; Save adjusted token value
            EX      DE,HL                ; Restore code string address
            CALL    GETINT               ; Get integer 0-255
            EX      DE,HL                ; Save code string address
            EX      (SP),HL              ; Save integer,HL = adj' token
            JP      GOFUNC               ; Jump to string function

FNVAL:      CALL    EVLPAR               ; Evaluate expression
            EX      (SP),HL              ; HL = Adjusted token value
            LD      DE,RETNUM            ; Return number from function
            PUSH    DE                   ; Save on stack
GOFUNC:     LD      BC,FNCTAB            ; Function routine addresses
            ADD     HL,BC                ; Point to right address
            LD      C,(HL)               ; Get LSB of address
            INC     HL                   ;
            LD      H,(HL)               ; Get MSB of address
            LD      L,C                  ; Address to HL
            JP      (HL)                 ; Jump to function

SGNEXP:     DEC     D                    ; Dee to flag negative exponent
            CP      ZMINUS               ; '-' token ?
            RET     Z                    ; Yes - Return
            CP      '-'                  ; '-' ASCII ?
            RET     Z                    ; Yes - Return
            INC     D                    ; Inc to flag positive exponent
            CP      '+'                  ; '+' ASCII ?
            RET     Z                    ; Yes - Return
            CP      ZPLUS                ; '+' token ?
            RET     Z                    ; Yes - Return
            DEC     HL                   ; DEC 'cos GETCHR INCs
            RET                          ; Return "NZ"

POR:        DB      0F6H                 ; Flag "OR"
PAND:       XOR     A                    ; Flag "AND"
            PUSH    AF                   ; Save "AND" / "OR" flag
            CALL    TSTNUM               ; Make sure it's a number
            CALL    DEINT                ; Get integer -32768 to 32767
            POP     AF                   ; Restore "AND" / "OR" flag
            EX      DE,HL                ; <- Get last
            POP     BC                   ; <-  value
            EX      (SP),HL              ; <-  from
            EX      DE,HL                ; <-  stack
            CALL    FPBCDE               ; Move last value to FPREG
            PUSH    AF                   ; Save "AND" / "OR" flag
            CALL    DEINT                ; Get integer -32768 to 32767
            POP     AF                   ; Restore "AND" / "OR" flag
            POP     BC                   ; Get value
            LD      A,C                  ; Get LSB
            LD      HL,ACPASS            ; Address of save AC as current
            JP      NZ,POR1              ; Jump if OR
            AND     E                    ; "AND" LSBs
            LD      C,A                  ; Save LSB
            LD      A,B                  ; Get MBS
            AND     D                    ; "AND" MSBs
            JP      (HL)                 ; Save AC as current (ACPASS)

POR1:       OR      E                    ; "OR" LSBs
            LD      C,A                  ; Save LSB
            LD      A,B                  ; Get MSB
            OR      D                    ; "OR" MSBs
            JP      (HL)                 ; Save AC as current (ACPASS)

TSTRED:     LD      HL,CMPLOG            ; Logical compare routine
            LD      A,(TYPE)             ; Get data type
            RRA                          ; Carry set = string
            LD      A,D                  ; Get last precedence value
            RLA                          ; Times 2 plus carry
            LD      E,A                  ; To E
            LD      D,64H                ; Relational precedence
            LD      A,B                  ; Get current precedence
            CP      D                    ; Compare with last
            RET     NC                   ; Eval if last was rel' or log'
            JP      STKTHS               ; Stack this one and get next
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
